sagdusmir/G32-Grill-Display-480x320-BTpref/misc/cases/Case JC3248W535C (remix) avoiding delemination with mounting option for G32 - 7295356/images/Case_JC3248W535C_with_bezel_optional_hanger.jpg

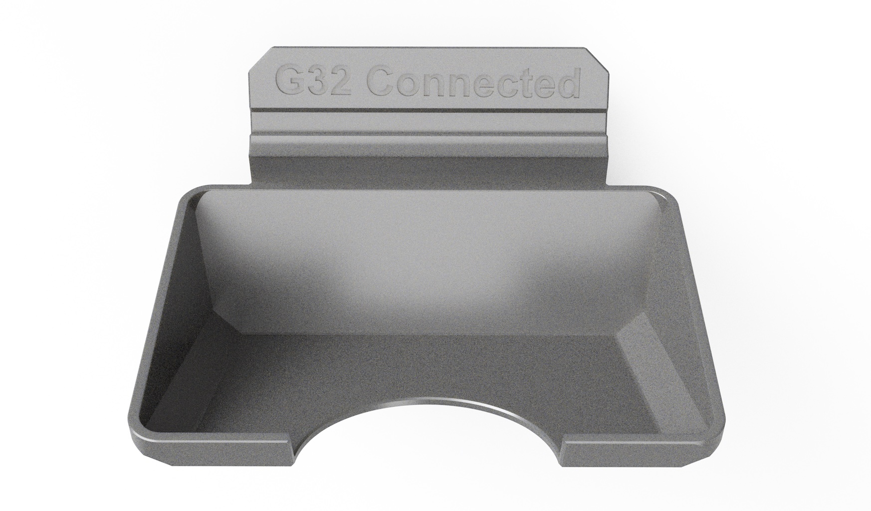
misc/cases/Case JC3248W535C (remix) avoiding delemination with mounting option for G32 - 7295356/images/Case_JC3248W535C_with_bezel_optional_hanger.jpg
