sagdusmir/G32-Grill-Display-480x320-BTpref/misc/cases/Case JC3248W535C (remix) avoiding delemination with mounting option for G32 - 7295356/images/IMG_0335.jpeg

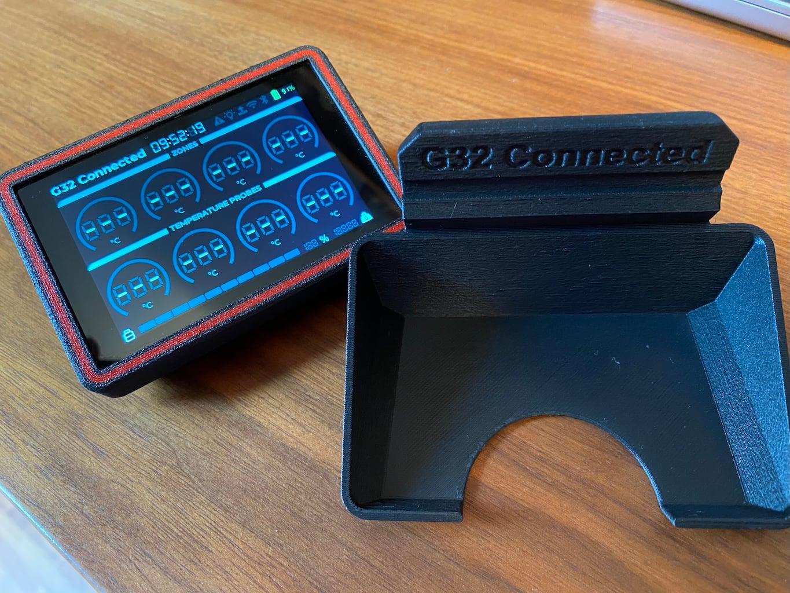
misc/cases/Case JC3248W535C (remix) avoiding delemination with mounting option for G32 - 7295356/images/IMG_0335.jpeg
