sagdusmir/G32-Grill-Display-480x320-BTpref/misc/cases/Case JC3248W535C (remix) with mounting option to G32 or compatible modules - 7182655/images/IMG_0139.jpeg

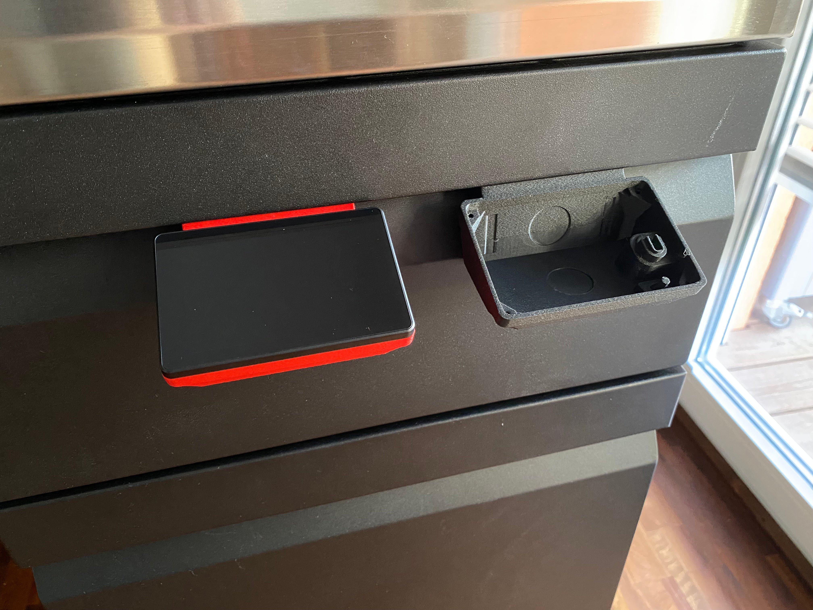
misc/cases/Case JC3248W535C (remix) with mounting option to G32 or compatible modules - 7182655/images/IMG_0139.jpeg
