sagdusmir/G32-Grill-Display-480x320-BTpref/misc/JC3248W535.jpeg

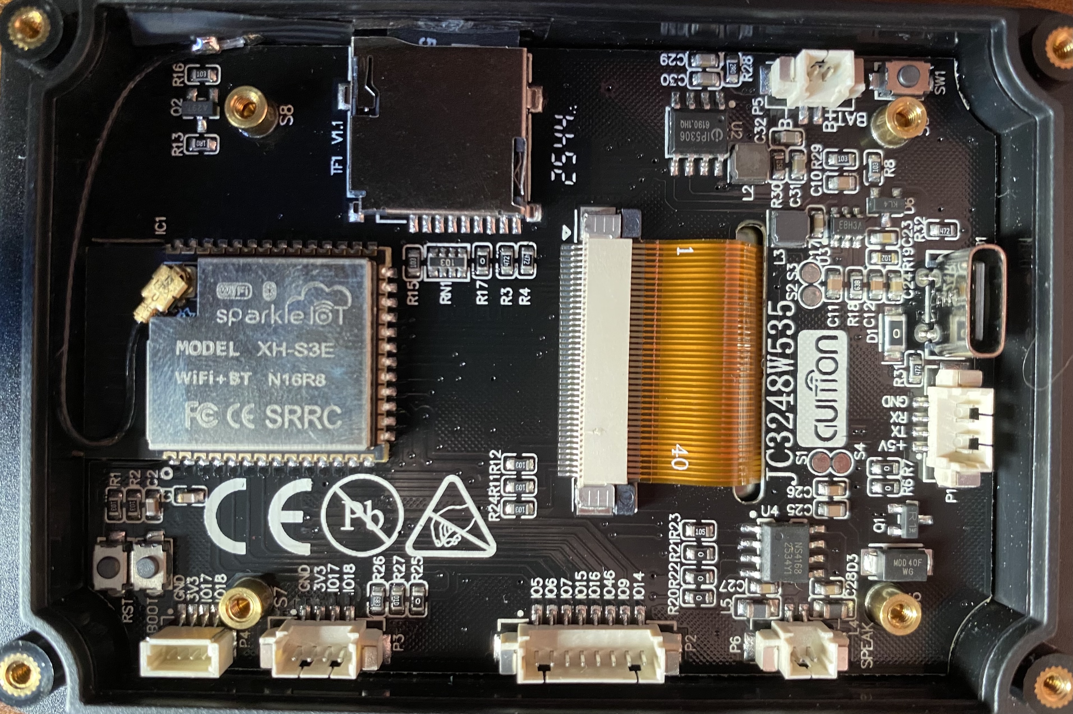
misc/JC3248W535.jpeg
