sagdusmir/G32-Grill-Display-480x320-BTpref/g32-display.yaml

substitutions:
  # # # # # # # # # # # # # # # # # # # # # # # # # # # # # # # # # # # # # # # # #
  # You will propably need to do changes only to the following lines (if at all): #
  # # # # # # # # # # # # # # # # # # # # # # # # # # # # # # # # # # # # # # # # #

  # Possible chages you might want to do to this yaml
  # -------------------------------------------------
  
  # api_encryption_key:
  # This can only changed by editing this file.
  # This value is required to connect your device to a Homa Assistant installation.
  # If you choose to change this value, you would need to do that every time you
  # upload a new software version. If you trust the other users of your WiFi, this
  # is probably unnecessary because this software does not create a fallback Access Point
  # with a default password.

  # ota_password:
  # This CAN be changed afterwards (not recommended) but any malicious attacker would need
  # to have access to your WiFi.
  # If you changed that value on the device, you will need to also update the value in this file
  # to get OTA updates working. The device uses this value as a default but also remembers the
  # last setting.
  # Same as above: only bother changing it if you really feel the need to do so.

  # FORCE_SHADOW_COLOR_TO_BLACK:
  # If the "shadow" of icons and numerical values annoy you, set this to 'true' to make it
  # disappear for all color schemes.
  # The color scheme "white (clean)" gives you an example how this would look like.

  # COLOR_SCHEMES
  # You can add your own color scheme – or remove existing ones that you don't like.
  # Columns are explained right above the COLOR_SCHEMES substitution.
  
  # General information for customizing optional hardware:
  # Speaker / Buzzer:
  # By default the buzzer is pre-configured. See two config blocks "RTTTL buzzer (GPIO pin)".
  # Configuration for a speaker is disabled. See two config blocks "RTTTL speaker (speaker header, external DAC)"
  # Just (un-)/comment the config blocks for the hardware you would like to use.

  # Name of the ESPHome device (modify if you like, avoid special characters)
  name: g32-display-bt90
  device_description: "Monitor an OW G32 grill"
  version: "BTpref-retro 2.5.7-1"
  url_qrcode: "https://github.com/sagdusmir/G32-Grill-Display-480x320-BTpref"
  url_check_for_updates: "https://api.github.com/repos/sagdusmir/G32-Grill-Display-480x320-BTpref/releases/latest"

  # Enter data of the newly created Home Assistant ESPHome device. Example:
  api_encryption_key: "E1fyywUUE1DWzu0OzhDkyc4yAnfGwyEfsVNvhytrU6k="

  # over-the-air updates (ESPHome CLI or Home Assistant add-On)
  # Hint: if you changed this value on the device, you might have to alter
  # this value here to match it. esphome cli uses the value from the yaml for the ota update!
  ota_password: "7fdf9f656d36180bfba92d596c9e7db3"

  # Some color themes:
  #
  # All consist of a primary color and three additional
  # colors of reduced luminocity.
  # -> color_100, ... color_25
  #
  # The next one lets you define a dedicated color for shadows of symbols and text.
  # Set this color as dark as you need. To have this set to black for all color schemes
  # simply use the FORCE_SHADOW_COLOR_TO_BLACK substitution.
  # -> color_00
  #
  # In addition to that, there is a "good" and a "bad"
  # color. For a less colorful UI you could just use
  # the primary color for "good", too. But I suggest
  # having a popping color for the "bad" stuff.
  # -> color_good, color_bad
  #
  # Last but not least, there is a separate color for
  # the light bulb symbol...which I usually do not change.
  # -> color_light
  #
  # The idx column is important and used to identify the select color theme.

  COLOR_SCHEMES: |
    //                  idx 100%      75%       50%       25%       <=25%    GOOD      BAD       LIGHT
    {
      {"white",         {0, 0xffffff, 0xbfbfbf, 0x808080, 0x404040, 0x404040, 0x8bff85, 0xff5757, 0xffff00}},
      {"amber",         {1, 0xffb900, 0xbd8a00, 0x805d00, 0x392900, 0x392900, 0x58b100, 0xff5600, 0xffff00}},
      {"cyan",          {2, 0x68e2fb, 0x00acbf, 0x007582, 0x003c43, 0x003c43, 0x75fb8a, 0xea838d, 0xffff00}},
      {"night red",     {3, 0xff0059, 0xc00044, 0x80002e, 0x400018, 0x400018, 0xff0059, 0xe4d300, 0xffff00}},
      {"green",         {4, 0x06bd00, 0x058d00, 0x046f00, 0x003008, 0x003008, 0x00ff00, 0xfe3a03, 0xffff00}},
      {"night blue",    {5, 0x1a00ff, 0x1300b6, 0x0d007a, 0x040028, 0x040028, 0x00ff4d, 0xff0092, 0xffff00}},
      {"purple",        {6, 0xff00e4, 0xc000ac, 0x800073, 0x32002d, 0x32002d, 0x00ffb0, 0xff1100, 0xffff00}},
      {"yellow",        {7, 0xffda00, 0xbea300, 0x806d00, 0x262000, 0x262000, 0x64dc00, 0xff5900, 0xffff00}},
      {"white (clean)", {8, 0xffffff, 0xbfbfbf, 0x808080, 0x404040, 0x000000, 0x8bff85, 0xff5757, 0xffff00}}
    }

  FORCE_SHADOW_COLOR_TO_BLACK: 'false'  # standard: use COLOR_00 for shadows
  # FORCE_SHADOW_COLOR_TO_BLACK: 'true'  # alternative: symbol and text shadows should not be visible

  # max temperature for zones and sensors
  Zone_Max: "500"
  Sensor_Max: "100"

  # interval for alarm sound
  Beeper_interval: "5s"

  # Meater protection alerts
  meater_tip_alert: '100'  # Specs: 100°C (original Meater: 100°C, 105°C (Meater PRO - not supported yet)
  meater_ambient_alert: '270'  # Specs: 275°C (original Meater), 550°C (Meater PRO - not supported yet)

  # sounds (in RTTTL syntax):
  G32_Connect_Sound: "pling2:d=16,o=6,b=140:e6,32p,d6"
  G32_Disconnect_Sound: "siren:d=8,o=5,b=100:d,e,d,e,d,e,d,e"
  MT_Connect_Sound: "Pling4:d=16,o=5,b=100:a5,32p,a6"
  MT_Disconnect_Sound: "plonk:d=16,o=5,b=100:a6,32p,a5"
  Wifi_Connect_Sound: "dadi:d=16,o=6,b=140:d6,32p,e6"
  Wifi_Disconnect_Sound: "siren:d=8,o=5,b=100:d,e,d,e,d,e,d,e"
  Timer_Alarm_Sound: "didididi:d=16,o=6,b=140:e6,32p,e6,32p,e6,32p,e6"
  Zone_Limit_Alarm_Sound: "dadidadi:d=8,o=5,b=150:d,e,d,e,d,e,d,e"
  Sensor_Limit_Alarm_Sound: "didadida:d=8,o=5,b=150:e,d,e,d,e,d,e,d"
  New_MAC_Sound: "click:d=32,o=6,b=120:32c,32p"

  # D A N G E R  Z O N E! # # # # # # # # # # # # # # # # # # # # # # # # # # # # 
  # From here on, please only make changes if you know what you are doing and   #
  # have an idea of what you want to achieve. :)                                #
  # # # # # # # # # # # # # # # # # # # # # # # # # # # # # # # # # # # # # # # #

  g32_mac_address: 94:E6:86:00:00:00
  g32_service_uuid: dc0f41ea-b6ae-46a8-a19e-1a3bf4342bcb
  g32_characteristic_uuid_tx: 'dc0f41e2-b6ae-46a8-a19e-1a3bf4342bcb'
  # g32_characteristic_uuid_rx: 'dc0f41e1-b6ae-46a8-a19e-1a3bf4342bcb'  # from the original OW app

  wifi_ssid: "wifi_ssid"
  wifi_password: "password"

  meater_mac_address: B8:1F:5E:00:00:00
  meater_service_uuid: 'a75cc7fc-c956-488f-ac2a-2dbc08b63a04'
  meater_characteristic_uuid_temp: '7edda774-045e-4bbf-909b-45d1991a2876'
  meater_characteristic_uuid_battery: '2adb4877-68d8-4884-bd3c-d83853bf27b8'

  Invalid_Sensor_Value: '1500'  # 1500 (and above) means "invalid"

  # shades of white (initial start values since substitutions work best)
  COLOR_100:   "0xffffff"  # 100% brightness
  COLOR_75:    "0xbfbfbf"  #  75%
  COLOR_50:    "0x808080"  #  50%
  COLOR_25:    "0x404040"  #  25%
  COLOR_00:    "0x404040"  # shadows
  COLOR_GOOD:  "0x8bff85"
  COLOR_BAD:   "0xff5757"
  COLOR_LIGHT: "0xffff00"

  # MEATER tip raw is 12-bit two's complement, little-endian. °C = (raw + 8) / 16.
  # Unsigned 0x0FE8 is 255°C; sign-extended it is -1°C. A 16-bit signed payload
  # (0xFFE8) is already negative after the int16_t cast, so leave it alone.
  meater_decode_tip: |-
    uint16_t tip_u = uint16_t(x[0]) | (uint16_t(x[1]) << 8); int16_t tip = int16_t(tip_u); if (tip_u < 0x1000 && tip >= 2048) tip -= 4096;

esphome:
  name: ${name}
  build_path: /tmp/esphome_build/${name}
  min_version: "2026.8.2"
  platformio_options:
    upload_speed: 921600
    board_build.flash_mode: dio
    board_build.f_flash: 80000000L
    board_build.f_cpu: 240000000L

  project:
    name: "g32.bt_display480_320"
    version: ${version}

  on_boot:
    priority: 1100 # stay above 1000 and below 1500!
    then:
      - lambda: id(boot_start_time) = millis();
                // the following line prevents the wifi password
                // from being shown - but makes it nearly impossible
                // to enter a complex password at all.
                // lv_textarea_set_password_show_time(id(settings_wifi_password_textarea), 0);  # 0 ms = hide immediately

esp32:
  board: esp32-s3-devkitc-1
  # variant: esp32S3  # use either board: or variant
  flash_size: 16MB
  cpu_frequency: 160MHZ  # esphome 2026.4.0 uses by default 240MHZ
  framework:
    type: esp-idf
    sdkconfig_options:
      # CONFIG_ESP_TASK_WDT_EN: "n" # Disables Task Watchdog Timer (TWDT)
      CONFIG_ESP_INT_WDT: "n"      # Disables Interrupt Watchdog Timer (IWDT)
      # COMPILER_OPTIMIZATION_SIZE: "y"  # optimize for size
      CONFIG_COMPILER_OPTIMIZATION_PERF: "y"
      CONFIG_ESP32S3_DEFAULT_CPU_FREQ_240: "y"
      CONFIG_ESP32S3_DATA_CACHE_64KB: "y"
      CONFIG_ESP32S3_DATA_CACHE_LINE_64B: "y"
      CONFIG_SPIRAM_FETCH_INSTRUCTIONS: "y"
      CONFIG_SPIRAM_RODATA: "y"
      CONFIG_ESP_WIFI_TASK_CORE_ID: "0"
      CONFIG_BT_BTC_TASK_CORE_ID: "0"
      CONFIG_BT_NIMBLE_PINNED_TO_CORE: "0"
      CONFIG_TCPIP_TASK_CORE_ID: "0"
      CONFIG_ESP_TIMER_TASK_CORE_ID: "0"
      CONFIG_ESP_MAIN_TASK_AFFINITY_CPU1: "y"

psram:
  mode: octal
  speed: 80MHz # 120mhz is not supported and falls back to 40mhz

logger:
  # baud_rate: 921600  # enable logging
  baud_rate: 0  # no logging -> saves power

api: # enable Home Assistant API
  encryption:
    key: ${api_encryption_key}
  reboot_timeout: 0s  

http_request:
  # optional global defaults (recommended for reliability)
  timeout: 5s
  verify_ssl: true
  follow_redirects: true

ota:
  - platform: esphome
    id: my_ota
    password: ${ota_password}

wifi:
  id: my_wifi
  ssid: ${wifi_ssid}  # must be dynamically applied later
  password: ${wifi_password}  # must be dynamically applied later
  fast_connect: True
  reboot_timeout: 0s
  on_connect:
    then:
      - rtttl.play: ${Wifi_Connect_Sound}
      - lambda: |-
          id(current_ip_address) = id(wifi_ip_sensor).state.c_str();
      - globals.set:
          id: wifi_connected
          value: 'true'
      - globals.set:
          id: apply_wifi_started_by_user
          value: 'false'
      - lvgl.widget.refresh: wifi_connect_label
      - lvgl.widget.refresh: current_wifi_ip_label
      - script.execute: check_for_updates

  on_disconnect:
    then:
      - if: # no sound if user updated credentials
          condition:
            - lambda: |-
                return !(id(apply_wifi_started_by_user));
          then:
            - rtttl.play: ${Wifi_Disconnect_Sound}
      - globals.set:
          id: wifi_connected
          value: 'false'
      - globals.set:
          id: current_ip_address
          value: '" "'  # not connected
      - lvgl.widget.refresh: wifi_connect_label
      - lvgl.widget.refresh: current_wifi_ip_label
esp32_ble:
  # 1xG32, 4xMeater probes -> maximum 5 connections needed
  max_connections: 5  # new option since 2025.10.15, used to be under the esp32_ble_tracker component

esp32_ble_tracker:
  # 1xG32, 4xMeater probes -> maximum 5 connections needed
  # max_connections: 5  # up till esphome 2025.9.1. now moved to esp32_ble component.
  on_ble_advertise:
    then:
      - lambda: |-
          char mac_buf[MAC_ADDRESS_PRETTY_BUFFER_SIZE];

          if (x.get_name().starts_with("OWG-G32C") && id(ble_g32_scan_started_by_user)) {
            x.address_str_to(mac_buf);
            id(settings_g32_mac_address) = mac_buf;
            lv_obj_clear_flag(id(settings_mac_address_updated), LV_OBJ_FLAG_HIDDEN);
            id(my_rtttl).play("${New_MAC_Sound}");
            ESP_LOGI("ble_adv", "G32 MAC address: %s", mac_buf);
            id(ble_g32_scan_stop).execute();
          }

          if ((x.get_name() == "MEATER" || x.get_name() == "MEATER+") && id(ble_meater_scan_started_by_user)) {
            if (id(ble_meaters_found) < 15) {
              if (!x.get_manufacturer_datas().empty() && !x.get_manufacturer_datas()[0].data.empty()) {  // assert data is available
                int probe_id = x.get_manufacturer_datas()[0].data[0];  // first data byte

                // for solo meaters without probe ID (issue reported by @JBecker32)
                if (probe_id == 0) {
                  probe_id = 1;
                }

                if (probe_id > 0 && probe_id < 5) {
                  int idx = probe_id-1;
                  if ((id(ble_meaters_found) & (1 << idx)) == 0) {
                    id(ble_meaters_found) |= (1 << idx);
                    id(my_rtttl).play("${New_MAC_Sound}");
                    x.address_str_to(mac_buf);
                    ESP_LOGI("ble_adv", "Meater MAC address: %s", mac_buf);
                    id(settings_meater_mac_addresses)[idx] = mac_buf;
                    std::array<lv_obj_t *, 4> meater_labels = {id(settings_meater0_label), id(settings_meater1_label), id(settings_meater2_label), id(settings_meater3_label)};
                    std::array<lv_obj_t *, 4> meater_updated = {id(settings_meater0_updated), id(settings_meater1_updated), id(settings_meater2_updated), id(settings_meater3_updated)};
                    lv_obj_clear_flag(meater_updated[idx], LV_OBJ_FLAG_HIDDEN);
                    lv_label_set_text(meater_labels[idx], mac_buf);
                  }
                }
              }
            }
            if (id(ble_meaters_found) >= 15) {
              id(ble_meater_scan_stop).execute();           
            }
          } 

          // some logging
          // if (x.get_name().starts_with("OWG-G32C")) {
          //   ESP_LOGI("ble_adv", "G32 found");
          //   ESP_LOGI("ble_adv", "  Name: %s", x.get_name().c_str());
          //   ESP_LOGI("ble_adv", "  MAC address: %s", x.address_str_to(mac_buf));
          // }
          // if (x.get_name().starts_with("MEATER+")) {
          //   ESP_LOGI("ble_adv", "Meater+ found");
          //   ESP_LOGI("ble_adv", "  Name: %s", x.get_name().c_str());
          //   ESP_LOGI("ble_adv", "  MAC address: %s", x.address_str_to(mac_buf));
          // }
          // if (x.get_name() == "MEATER") {
          //   ESP_LOGI("ble_adv", "Meater found");
          //   ESP_LOGI("ble_adv", "  Name: %s", x.get_name().c_str());
          //   ESP_LOGI("ble_adv", "  MAC address: %s", x.address_str_to(mac_buf));
          // }
          // if (x.get_name() == "MEATER BLOCK") {
          //   ESP_LOGI("ble_adv", "Meater Block found");
          //   ESP_LOGI("ble_adv", "  Name: %s", x.get_name().c_str());
          //   ESP_LOGI("ble_adv", "  MAC address: %s", x.address_str_to(mac_buf));
          // }

          // log everything we get on advertise
          if (0) {
            ESP_LOGD("ble_adv", "New BLE device");
            ESP_LOGD("ble_adv", "  address: %s", x.address_str_to(mac_buf));
            ESP_LOGD("ble_adv", "  RSSI: %d", x.get_rssi());
            ESP_LOGD("ble_adv", "  name: %s", x.get_name().c_str());
            ESP_LOGD("ble_adv", "  Advertised service UUIDs:");
            for (auto uuid : x.get_service_uuids()) {
              char uuid_buf[37];
              ESP_LOGD("ble_adv", "    - %s", uuid.to_str(uuid_buf));
            }
            ESP_LOGD("ble_adv", "  Advertised service data:");
            for (auto data : x.get_service_datas()) {
              char uuid_buf[37];
              ESP_LOGD("ble_adv", "    - %s: (length %i)", data.uuid.to_str(uuid_buf), data.data.size());
              // To log the actual data bytes, you can add a loop here
              std::string hex_data;
              for (auto byte : data.data) {
                  char buf[3];
                  sprintf(buf, "%02X ", byte);
                  hex_data += buf;
                }
              ESP_LOGD("ble_adv", "      data: %s", hex_data.c_str());
            }
            ESP_LOGD("ble_adv", "  Advertised manufacturer data:");
            for (auto data : x.get_manufacturer_datas()) {
              char uuid_buf[37];
              ESP_LOGD("ble_adv", "    - %s: (length %i)", data.uuid.to_str(uuid_buf), data.data.size());
              // Similarly, log the data bytes
              std::string hex_data;
              for (auto byte : data.data) {
                  char buf[3];
                  sprintf(buf, "%02X ", byte);
                  hex_data += buf;
                }
              ESP_LOGD("ble_adv", "      data: %s", hex_data.c_str());
            }
          }


      - lvgl.widget.refresh: settings_mac_address_label
      - lvgl.widget.refresh: [settings_meater0_label, settings_meater1_label, settings_meater2_label, settings_meater3_label]

ble_client:
  - mac_address: ${g32_mac_address}  # must be dynamically applied later
    id: ow_g32
    on_connect:
      then:
        - rtttl.play: ${G32_Connect_Sound}
        - globals.set:
            id: g32_connected
            value: 'true'
        - lvgl.widget.refresh: g32bt_connect_label
    on_disconnect:
      then:
        - rtttl.play: ${G32_Disconnect_Sound}
        - globals.set:
            id: g32_connected
            value: 'false'
        - lvgl.widget.refresh: g32bt_connect_label
        - globals.set:
            id: gas_weight
            value: '-1'
        - lvgl.widget.refresh: gas_weight_label
        - globals.set:
            id: gas_percent
            value: '0'
        - lvgl.widget.refresh: [gas_percent_label, gas_percent_label_unit, gas_percent_bar]
        - globals.set:
            id: zone1_value
            value: ${Invalid_Sensor_Value}
        - globals.set:
            id: zone2_value
            value: ${Invalid_Sensor_Value}
        - globals.set:
            id: zone3_value
            value: ${Invalid_Sensor_Value}
        - globals.set:
            id: zone4_value
            value: ${Invalid_Sensor_Value}
        - globals.set:
            id: sensor1_value
            value: ${Invalid_Sensor_Value}
        - globals.set:
            id: sensor2_value
            value: ${Invalid_Sensor_Value}
        - globals.set:
            id: sensor3_value
            value: ${Invalid_Sensor_Value}
        - globals.set:
            id: sensor4_value
            value: ${Invalid_Sensor_Value}
        - globals.set:
            id: active_sensors
            value: "0"
        - script.execute: refresh_all_temps

  - mac_address: ${meater_mac_address}
    id: meater0
    on_connect:
      then:
        - lambda: |-
            id(active_meaters) |= 0x01;
            id(meater_alarms_tip) |= 0x01;
            id(meater_alarms_ambient) |= 0x01;
        - rtttl.play: ${MT_Connect_Sound}
    on_disconnect:
      then:
        - lambda: |-
            id(active_meaters) &= ~0x01;
            id(meater_alarms_tip) &= ~0x01;
            id(meater_alarms_ambient) &= ~0x01;
        - lambda: |-
            id(g32_probe1).publish_state(${Invalid_Sensor_Value});
        - rtttl.play: ${MT_Disconnect_Sound}
        - script.execute: refresh_all_meater_alerts
  - mac_address: ${meater_mac_address}
    id: meater1
    on_connect:
      then:
        - lambda: |-
            id(active_meaters) |= 0x02;
            id(meater_alarms_tip) |= 0x02;
            id(meater_alarms_ambient) |= 0x02;
        - rtttl.play: ${MT_Connect_Sound}
    on_disconnect:
      then:
        - lambda: |-
            id(active_meaters) &= ~0x02;
            id(meater_alarms_tip) &= ~0x02;
            id(meater_alarms_ambient) &= ~0x02;
        - lambda: |-
            id(g32_probe2).publish_state(${Invalid_Sensor_Value});
        - rtttl.play: ${MT_Disconnect_Sound}
        - script.execute: refresh_all_meater_alerts
  - mac_address: ${meater_mac_address}
    id: meater2
    on_connect:
      then:
        - lambda: |-
            id(active_meaters) |= 0x04;
            id(meater_alarms_tip) |= 0x04;
            id(meater_alarms_ambient) |= 0x04;
        - rtttl.play: ${MT_Connect_Sound}
    on_disconnect:
      then:
        - lambda: |-
            id(active_meaters) &= ~0x04;
            id(meater_alarms_tip) &= ~0x04;
            id(meater_alarms_ambient) &= ~0x04;
        - lambda: |-
            id(g32_probe3).publish_state(${Invalid_Sensor_Value});
        - rtttl.play: ${MT_Disconnect_Sound}
        - script.execute: refresh_all_meater_alerts
  - mac_address: ${meater_mac_address}
    id: meater3
    on_connect:
      then:
        - lambda: |-
            id(active_meaters) |= 0x08;
            id(meater_alarms_tip) |= 0x08;
            id(meater_alarms_ambient) |= 0x08;
        - rtttl.play: ${MT_Connect_Sound}
    on_disconnect:
      then:
        - lambda: |-
            id(active_meaters) &= ~0x08;
            id(meater_alarms_tip) &= ~0x08;
            id(meater_alarms_ambient) &= ~0x08;
        - lambda: |-
            id(g32_probe4).publish_state(${Invalid_Sensor_Value});
        - rtttl.play: ${MT_Disconnect_Sound}
        - script.execute: refresh_all_meater_alerts

#-------------------------------------------
# Display qspi
#-------------------------------------------
spi:
  id: display_qspi
  type: quad
  clk_pin: 47
  data_pins: [21, 48, 40, 39]

display:
  # - platform: mipi_spi
  #   model: axs15231  # JC4832W535 or axs15231 / JC3248W535C variant
  - platform: qspi_dbi
    model: JC4832W535
    data_rate: 40MHz
    id: my_display
    spi_id: display_qspi
    dimensions:
      height: 480
      width: 320
    cs_pin:
      number: 45
      ignore_strapping_warning: true
    auto_clear_enabled: false  # has to be set to 'false' for lvgl
    update_interval: never  # LVGL handles rendering

#-------------------------------------------
# Touchscreen gt911 i2c
#-------------------------------------------
i2c:
  - id: touchscreen_bus
    sda: GPIO4
    scl: GPIO8
    scan: false

touchscreen:
  - platform: axs15231
    id: my_touchscreen
    display: my_display
    i2c_id: touchscreen_bus
    # for test purposes, touch coordinates can be logged
    # on_touch:
    #   - lambda: |-
    #       ESP_LOGI("cal", "x=%d, y=%d, x_raw=%d, y_raw=%0d",
    #         touch.x,
    #         touch.y,
    #         touch.x_raw,
    #         touch.y_raw
    #       );
    on_release:
      - if:
          condition: lvgl.is_paused
          then:
            - logger.log: "Display is resuming"
            - lvgl.resume:
            - lvgl.widget.redraw:
            - light.turn_on: backlight

#---------------------------------------------
# RTTTL speaker (speaker header, external DAC)
#---------------------------------------------
# i2s_audio:                               # variant [speaker] 
#   # external DAC: NS4168                 # variant [speaker] 
#   i2s_lrclk_pin: GPIO02                  # variant [speaker] 
#   i2s_bclk_pin: GPIO42                   # variant [speaker] 
# speaker:                                 # variant [speaker] 
#   - platform: i2s_audio                  # variant [speaker]
#     id: my_speaker                       # variant [speaker] 
#     dac_type: external                   # variant [speaker] 
#     i2s_dout_pin: GPIO41                 # variant [speaker] 
#     channel: mono                        # variant [speaker] 
#     buffer_duration: 0.1s                # variant [speaker] 
#-------------------------------------------
# Internal outputs
#-------------------------------------------
output:
  - platform: ledc
    id: gpio_backlight_pwm
    pin: 1


    #-------------------------------------------
    # RTTTL buzzer (GPIO pin)
    #-------------------------------------------
  - id: helper_low_beeper              # variant [buzzer]
    platform: ledc                     # variant [buzzer]
    pin: 14                            # variant [buzzer]
  - platform: ledc                     # variant [buzzer]
    pin: 9                             # variant [buzzer]
    id: rtttl_out                      # variant [buzzer]
#-------------------------------------------
# Internal lights
#-------------------------------------------
light:
  - id: backlight
    name: Backlight
    platform: monochromatic
    output: gpio_backlight_pwm
    restore_mode: ALWAYS_ON

rtttl:
  id: my_rtttl

  #-------------------------------------------
  # RTTTL buzzer (GPIO pin)
  #-------------------------------------------
  output: rtttl_out                      # variant [buzzer]
  gain: 80%                              # variant [buzzer]

  #-------------------------------------------
  # RTTTL speaker (speaker header, external DAC)
  #-------------------------------------------
  # speaker: my_speaker                    # variant [speaker] 
  # gain: 100%                             # variant [speaker] 
interval:
  - interval: 1s
    then:
      - script.execute: timer_update
  - interval: 10s
    then:
      - lvgl.widget.refresh: warning_on_label
  - interval: ${Beeper_interval}
    then:
      - lambda: |-
          if( ((id(zone1_limit_value) > 0) && (id(zone1_value) >= id(zone1_limit_value)))
           || ((id(zone2_limit_value) > 0) && (id(zone2_value) >= id(zone2_limit_value)))
           || ((id(zone3_limit_value) > 0) && (id(zone3_value) >= id(zone3_limit_value)))
           || ((id(zone4_limit_value) > 0) && (id(zone4_value) >= id(zone4_limit_value)))
           || id(meater_alarms_ambient) > 0 || id(meater_alarms_tip) > 0 ) {
            id(my_rtttl).play("${Zone_Limit_Alarm_Sound}");
          }
          else if ( ((id(sensor1_limit_value) > 0) && (id(sensor1_value) >= id(sensor1_limit_value)))
                 || ((id(sensor2_limit_value) > 0) && (id(sensor2_value) >= id(sensor2_limit_value)))
                 || ((id(sensor3_limit_value) > 0) && (id(sensor3_value) >= id(sensor3_limit_value)))
                 || ((id(sensor4_limit_value) > 0) && (id(sensor4_value) >= id(sensor4_limit_value))) ) {
            id(my_rtttl).play("${Sensor_Limit_Alarm_Sound}");
          }
          else if( id(timer_alarm) == true ) {
            id(my_rtttl).play("${Timer_Alarm_Sound}");
          }
  - interval: 1s
    then:
      - if:
          condition:
            and:
              - lambda: return !id(boot_screen_color_scheme_init);
          then:
            - lambda: |-
                id(boot_screen_color_scheme_init) = true;
                id(settings_color_scheme_idx) = id(settings_color_scheme_idx_persistent);
                id(apply_color_scheme).execute();

      - if:
          condition:
            and:
              - lambda: 'return !id(boot_screen_hidden);'
              - lambda: 'return millis() - id(boot_start_time) >= 2000;'
          then:
            - script.execute: hide_boot_screen

#-------------------------------------------
# Global varaibles
#-------------------------------------------
globals:
  - id: wifi_connected
    type: bool
    initial_value: 'false'
  - id: g32_connected
    type: bool
    initial_value: 'false'
  - id: firebox_open
    type: bool
    initial_value: 'false'
  - id: light_on
    type: bool
    initial_value: 'false'
  - id: warning_on
    type: bool
    initial_value: 'false'
  - id: gas_weight
    type: int32_t
    initial_value: '-1'
  - id: gas_percent
    type: int32_t
    initial_value: '0'
  - id: ble_g32_scan_started_by_user  # for managing "scan" button status
    type: bool
    initial_value: 'false'
  - id: ble_meater_scan_started_by_user  # for managing "scan" button status
    type: bool
    initial_value: 'false'
  - id: ble_meaters_found  # bits set/reset for every active/inactive Meater probe
    type: int
    initial_value: '0'
  - id: apply_wifi_started_by_user  # for supressing sounds
    type: bool
    initial_value: 'false'
  - id: flag_wifi_updated  # helper to know if wifi needs to be applied
    type: bool
    initial_value: 'true'
  - id: flag_ota_updated  # helper to know if ota needs to be applied
    type: bool
    initial_value: 'true'

  - id: settings_wifi_ssid_persistent
    type: std::string
    restore_value: true
    initial_value: '"${wifi_ssid}"'
    max_restore_data_length: 33  # max SSID length: 32
  - id: settings_wifi_ssid
    type: std::string
    initial_value: " "
  - id: settings_wifi_password_persistent
    type: std::string
    restore_value: true
    initial_value: '"${wifi_password}"'
    max_restore_data_length: 65  # max password length: 64
  - id: settings_wifi_password
    type: std::string
    initial_value: " "
  - id: settings_ota_password_persistent
    type: std::string
    restore_value: true
    initial_value: '"${ota_password}"'
    max_restore_data_length: 65  # max password length: 64
  - id: settings_ota_password
    type: std::string
    initial_value: '""'

  - id: color_schemes
    type: std::map<std::string, std::vector<uint32_t>>
    initial_value: '${COLOR_SCHEMES}'
  - id: color_100
    type: int
    initial_value: '0x000000'
  - id: color_75
    type: int
    initial_value: '0x000000'
  - id: color_50
    type: int
    initial_value: '0x000000'
  - id: color_25
    type: int
    initial_value: '0x000000'
  - id: color_00
    type: int
    initial_value: '0x000000'
  - id: color_good
    type: int
    initial_value: '0x000000'
  - id: color_bad
    type: int
    initial_value: '0x000000'
  - id: color_light
    type: int
    initial_value: '0x000000'

  - id: boot_start_time
    type: uint32_t
    initial_value: '0'
  - id: boot_screen_hidden
    type: bool
    initial_value: 'false'
  - id: boot_screen_color_scheme_init
    type: bool
    initial_value: 'false'
  - id: latest_version
    type: std::string
    initial_value: '"${version}"'

  - id: active_sensors      # bits set/reset for every active/inactive Sensor
    type: int
    initial_value: '0'

  - id: active_meaters      # bits set/reset for every active/inactive Meater probe
    type: int
    initial_value: '0'

  - id: zone1_value         # the value used for zone temperature labels and arcs
    type: int
    initial_value: ${Invalid_Sensor_Value}
  - id: zone2_value
    type: int
    initial_value: ${Invalid_Sensor_Value}
  - id: zone3_value
    type: int
    initial_value: ${Invalid_Sensor_Value}
  - id: zone4_value
    type: int
    initial_value: ${Invalid_Sensor_Value}

  - id: sensor1_value       # the value used for sensor temperature labels and arcs
    type: int
    initial_value: ${Invalid_Sensor_Value}
  - id: sensor2_value
    type: int
    initial_value: ${Invalid_Sensor_Value}
  - id: sensor3_value
    type: int
    initial_value: ${Invalid_Sensor_Value}
  - id: sensor4_value
    type: int
    initial_value: ${Invalid_Sensor_Value}

  - id: zone1_limit_value   # the value used for zone limit labels and arcs
    type: int
    initial_value: '0'
  - id: zone2_limit_value
    type: int
    initial_value: '0'
  - id: zone3_limit_value
    type: int
    initial_value: '0'
  - id: zone4_limit_value
    type: int
    initial_value: '0'

  - id: sensor1_limit_value # the value used for sensor limit labels and arcs
    type: int
    initial_value: '0'
  - id: sensor2_limit_value
    type: int
    initial_value: '0'
  - id: sensor3_limit_value
    type: int
    initial_value: '0'
  - id: sensor4_limit_value
    type: int
    initial_value: '0'

  - id: meater_values_tip
    type: std::array<float, 4>
    initial_value: '{0.0,0.0,0.0,0.0}'
  - id: meater_values_ambient
    type: std::array<float, 4>
    initial_value: '{0.0,0.0,0.0,0.0}'
  - id: meater_values_battery
    type: std::array<int, 4>
    initial_value: '{100,100,100,100}'


  - id: meater_tip_alert
    type: float
    initial_value: '${meater_tip_alert}'
  - id: meater_ambient_alert
    type: float
    initial_value: '${meater_ambient_alert}'
  - id: meater_alarms_tip  # bits set/reset
    type: int
    initial_value: '0'
  - id: meater_alarms_ambient  # bits set/reset
    type: int
    initial_value: '0'

  - id: battery_soc_value
    type: int
    initial_value: '0'

  - id: sensor_index        # parameter for zone (1-4) or sensor (5-8)
    type: int
    initial_value: '0'
  - id: sensor_limit_value  # the actual sensor limit for the indexed Zone/Sensor
    type: int
    initial_value: '0'
  - id: sensor_max_value    # maximum value for zone and sensor values (arcs)
    type: int
    initial_value: '0'

  - id: timer_h             # timer hours
    type: int
    initial_value: '0'
  - id: timer_m             # timer minutes
    type: int
    initial_value: '0'
  - id: timer_s             # timer seconds
    type: int
    initial_value: '0'
  - id: timer_active        # timer active (=running)
    type: bool
    initial_value: 'false'
  - id: timer_alarm         # timer alarm active
    type: bool
    initial_value: 'false'

  - id: helper_h             # timer hours
    type: int
    initial_value: '0'
  - id: helper_m             # timer minutes
    type: int
    initial_value: '0'
  - id: helper_s             # timer seconds
    type: int
    initial_value: '0'

  - id: last_sensor_lower_digits  # set limits page
    type: int
    initial_value: '0'

  # settings: persisted and temporary values
  # stick to the _persistent value for usage.
  # the temporary value is intended for the
  # settings page only.
  - id: settings_g32_mac_address_persistent
    type: std::string
    initial_value: '"${g32_mac_address}"' 
    restore_value: true
    max_restore_data_length: 17
  - id: settings_g32_mac_address
    type: std::string
    initial_value: ""

  - id: settings_meater_mac_addresses_persistent
    type: std::string
    initial_value: '"${meater_mac_address},${meater_mac_address},${meater_mac_address},${meater_mac_address}"'
    restore_value: true
    max_restore_data_length: 72
  - id: settings_meater_mac_addresses
    type: std::array<std::string, 4>
    initial_value: '{"00:00:00:00:00:00","00:00:00:00:00:00","00:00:00:00:00:00","00:00:00:00:00:00"}'

  - id: settings_min_gas_value_persistent
    type: int
    initial_value: "20"
    restore_value: true
  - id: settings_min_gas_value
    type: int
    initial_value: '0'
  - id: settings_min_soc_value_persistent
    type: int
    initial_value: "25"
    restore_value: true
  - id: settings_min_soc_value
    type: int
    initial_value: '0'
  - id: settings_hide_soc_persistent
    type: bool
    initial_value: 'false'
    restore_value: true
  - id: settings_hide_soc
    type: bool
    initial_value: 'false'
  - id: settings_hide_gas_level_persistent
    type: bool
    initial_value: 'false'
    restore_value: true
  - id: settings_hide_gas_level
    type: bool
    initial_value: 'false'
  - id: settings_enable_temperature_limits_persistent
    type: bool
    initial_value: 'true'
    restore_value: true
  - id: settings_enable_temperature_limits
    type: bool
    initial_value: 'true'
  - id: settings_enable_auto_hiding_temperature_limits_persistent
    type: bool
    initial_value: 'false'
    restore_value: true
  - id: settings_enable_auto_hiding_temperature_limits
    type: bool
    initial_value: 'false'
  - id: settings_hide_inactive_sensors_persistent
    type: bool
    initial_value: 'false'
    restore_value: true
  - id: settings_hide_inactive_sensors
    type: bool
    initial_value: 'false'
  - id: settings_show_time_persistent
    type: bool
    initial_value: 'true'
    restore_value: true
  - id: settings_show_time
    type: bool
    initial_value: 'true'
  - id: settings_hide_timer_persistent
    type: bool
    initial_value: 'false'
    restore_value: true
  - id: settings_hide_timer
    type: bool
    initial_value: 'false'
  - id: settings_display_timeout_value_persistent
    type: int
    initial_value: '0'
    restore_value: true
  - id: settings_display_timeout_value
    type: int
    initial_value: '0'
  - id: settings_color_scheme_idx_persistent
    type: int
    initial_value: '0'
    restore_value: true
  - id: settings_color_scheme_idx
    type: int
    initial_value: '0'

  - id: current_ip_address
    type: std::string
    initial_value: '" "'  # not connected

text_sensor:
  - platform: wifi_info
    ip_address:
      id: wifi_ip_sensor

  - platform: template
    name: "Software Version"
    lambda: |-
      return std::string("${version}");

font:
  - file: 'https://raw.githubusercontent.com/sagdusmir/G32-Grill-Display-480x320-BTpref/main/fonts/MaterialDesign-Webfont/materialdesignicons-webfont.ttf'
    # file: 'fonts/MaterialDesign-Webfont/materialdesignicons-webfont.ttf'
    id: ICON_FONT_24
    size: 24
    glyphs:
      - "\U000F05A9" # mdi-wifi
      - "\U000F00AF" # mdi-bluetooth
      - "\U000F12A3" # mdi-battery-high
      - "\U000F12A2" # mdi-battery-medium
      - "\U000F12A1" # mdi-battery-low
      - "\U000F008E" # mdi-battery-outline
      - "\U000F17E6" # mdi-battery-plus
      - "\U000F0208" # mdi-eye
      - "\U000F0238" # mdi-fire (used for meater)
      - "\U000F029A" # mdi-gauge
      - "\U000F1358" # mdi-propane-tank-outline
      - "\U000F002A" # mdi-alert-outline
      - "\U000F0DD0" # mdi-format-list-bulleted-square
      - "\U000F140B" # mdi-lightning-bolt
      - "\U000F050F" # mdi-thermometer
      - "\U000F1A4E" # mdi-lightbulb-on-20
      - "\U000F0D3F" # mdi-weight-grams
  - file: 'https://raw.githubusercontent.com/sagdusmir/G32-Grill-Display-480x320-BTpref/main/fonts/MaterialDesign-Webfont/materialdesignicons-webfont.ttf'
    # file: 'fonts/MaterialDesign-Webfont/materialdesignicons-webfont.ttf'
    id: ICON_FONT_18
    size: 18
    glyphs:
      - "\U000F15D7" # mdi mdi-fire-alert
  - file: 'https://raw.githubusercontent.com/sagdusmir/G32-Grill-Display-480x320-BTpref/main/fonts/MaterialDesign-Webfont/materialdesignicons-webfont.ttf'
    # file: 'fonts/MaterialDesign-Webfont/materialdesignicons-webfont.ttf'
    id: ICON_FONT_12
    size: 12
    glyphs:
      - "\U000F009A" # mdi-bell
  - file: 'https://raw.githubusercontent.com/sagdusmir/G32-Grill-Display-480x320-BTpref/main/fonts/MaterialDesign-Webfont/materialdesignicons-webfont.ttf'
    # file: 'fonts/MaterialDesign-Webfont/materialdesignicons-webfont.ttf'
    id: ICON_FONT_14
    size: 14
    glyphs:
      - "\U000F051B" # mdi-timer-outline
  - file: 'https://raw.githubusercontent.com/sagdusmir/G32-Grill-Display-480x320-BTpref/main/fonts/DESG07/DSEG7ClassicMini-Bold.ttf'
    # file: 'fonts/DESG07/DSEG7ClassicMini-Bold.ttf'
    id: SEGMENT_FONT_35
    size: 35
    glyphs:
      - "0"
      - "1"
      - "2"
      - "3"
      - "4"
      - "5"
      - "6"
      - "7"
      - "8"
      - "9"
      - "-"
      - " "
  - file: 'https://raw.githubusercontent.com/sagdusmir/G32-Grill-Display-480x320-BTpref/main/fonts/DESG07/DSEG7ClassicMini-Bold.ttf'
    # file: 'fonts/DESG07/DSEG7ClassicMini-Bold.ttf'
    id: SEGMENT_FONT_22
    size: 22
    glyphs:
      - "0"
      - "1"
      - "2"
      - "3"
      - "4"
      - "5"
      - "6"
      - "7"
      - "8"
      - "9"
      - "-"
      - " "
  - file: 'https://raw.githubusercontent.com/sagdusmir/G32-Grill-Display-480x320-BTpref/main/fonts/DESG07/DSEG7ClassicMini-Bold.ttf'
    # file: 'fonts/DESG07/DSEG7ClassicMini-Bold.ttf'
    id: SEGMENT_FONT_20
    size: 20
    glyphs:
      - "0"
      - "1"
      - "2"
      - "3"
      - "4"
      - "5"
      - "6"
      - "7"
      - "8"
      - "9"
      - "-"
      - "."
      - ":"
      - " "
  - file: 'https://raw.githubusercontent.com/sagdusmir/G32-Grill-Display-480x320-BTpref/main/fonts/DESG07/DSEG7ClassicMini-Bold.ttf'
    # file: 'fonts/DESG07/DSEG7ClassicMini-Bold.ttf'
    id: SEGMENT_FONT_14
    size: 14
    glyphs:
      - "0"
      - "1"
      - "2"
      - "3"
      - "4"
      - "5"
      - "6"
      - "7"
      - "8"
      - "9"
      - "-"
      - " "
  - file: 'https://raw.githubusercontent.com/sagdusmir/G32-Grill-Display-480x320-BTpref/main/fonts/DESG07/DSEG7ClassicMini-Bold.ttf'
    # file: 'fonts/DESG07/DSEG7ClassicMini-Bold.ttf'
    id: SEGMENT_FONT_8
    size: 8
    glyphs:
      - "0"
      - "1"
      - "2"
      - "3"
      - "4"
      - "5"
      - "6"
      - "7"
      - "8"
      - "9"
  - file: 'https://raw.githubusercontent.com/sagdusmir/G32-Grill-Display-480x320-BTpref/main/fonts/Montserrat/Montserrat-Bold.ttf'
    # file: 'fonts/Montserrat/Montserrat-Bold.ttf'
    id: MONTSERRAT_BOLD_FONT_22
    size: 22
    glyphs:
      - "G"
      - "3"
      - "2"
      - " "
      - "C"
      - "o"
      - "n"
      - "e"
      - "c"
      - "t"
      - "d"
  - file: 'https://raw.githubusercontent.com/sagdusmir/G32-Grill-Display-480x320-BTpref/main/fonts/Montserrat/Montserrat-Bold.ttf'
    # file: 'fonts/Montserrat/Montserrat-Bold.ttf'
    id: MONTSERRAT_BOLD_FONT_18
    size: 18
    glyphs:
      - "0"
      - "1"
      - "2"
      - "3"
      - "4"
      - "5"
      - "6"
      - "7"
      - "8"
      - "9"
      - " "
      - "-"
      - "("
      - ")"
      - "a"
      - "b"
      - "c"
      - "d"
      - "e"
      - "f"
      - "g"
      - "h"
      - "i"
      - "j"
      - "k"
      - "l"
      - "m"
      - "n"
      - "o"
      - "p"
      - "q"
      - "r"
      - "s"
      - "t"
      - "u"
      - "v"
      - "w"
      - "x"
      - "y"
      - "z"
  - file: 'https://raw.githubusercontent.com/sagdusmir/G32-Grill-Display-480x320-BTpref/main/fonts/Montserrat/Montserrat-Bold.ttf'
    # file: 'fonts/Montserrat/Montserrat-Bold.ttf'
    id: MONTSERRAT_BOLD_FONT_14
    size: 14
    glyphs:
      - "Z"
      - "O"
      - "N"
      - "E"
      - "S"
      - "R"
      - "T"
      - "M"
      - "P"
      - "A"
      - "U"
      - "B"
      - "I"
      - "W"
      - "C"
      - "D"
      - "L"
      - "G"
      - "1"
      - "2"
      - "3"
      - "4"
      - " "

#-------------------------------------------
# Time platform
#-------------------------------------------
time:
  id: my_time

  # use public ntp servers so we can get along without Home Assistant
  platform: sntp
  # alternatively
  # platform: homeassistant

  # timezone: "Europe/Berlin"  # should be detected automatically during build process
  on_time_sync:
    - script.execute: time_update
  on_time:
    - seconds: '*'
      then:
        - script.execute: time_update

#-------------------------------------------
# LVGL library for displays
#-------------------------------------------
lvgl:
  draw_rounding: 8 # necessary for the axs15231 display controller
  buffer_size: 50%
  displays: my_display
  touchscreens: my_touchscreen
  rotation: 90
  bg_color: 0
  border_width: 0
  outline_width: 0
  theme:
    label:
      bg_color: 0
      bg_opa: COVER
      width: 120
      text_align: CENTER
    bar:
      radius: 5
      indicator:
        radius: 5
        arc_color: red
    arc:
      radius: 5
      indicator:
        arc_rounded: false
        radius: 5
    roller:
      text_font: MONTSERRAT_20
      width: 60
      selected:
        text_font: MONTSERRAT_BOLD_FONT_18
    slider:
      bg_opa: COVER
      radius: 0
      adv_hittest: true
      border_width: 0
      indicator:
        radius: 0
      knob:
        radius: 2

    textarea:
      width: 340
      height: 30
      text_font: MONTSERRAT_18
      border_width: 1
    keyboard:
      text_color: ${COLOR_100}
      bg_color: ${COLOR_25}
      items:
        bg_color: ${COLOR_100}
        text_color: ${COLOR_25}

  style_definitions:
    - id: arc_value_style
      x: 8
      y: 15
      width: 104
      height: 104
      arc_opa: COVER
      arc_rounded: false
      arc_width: 6
    - id: arc_limit_style
      x: 13
      y: 21
      width: 94
      height: 94
      arc_opa: 100%
      arc_rounded: false
      arc_width: 3
      arc_color: 0
    - id: item_obj_style
      width: 120
      height: 120
      bg_color: 0
      pad_all: 0
      radius: 0
      outline_width: 0
      border_width: 0
      border_side: NONE
      outline_pad: 0

  # send display to idle state after timeout
  on_idle:
    timeout: !lambda "return(id(settings_display_timeout_value_persistent) * 1000);"
    then:
    - if:
        condition:
          - lambda: "return id(settings_display_timeout_value_persistent) > 0;"
        then:
          - logger.log: "Display is idle"
          - light.turn_off: backlight
          - lvgl.pause:

  # boot screen with spinner - just for fun
  top_layer:
    widgets:
      - obj:
          id: boot_screen
          x: 0
          y: 0
          width: 480
          height: 320
          bg_color: 0
          bg_opa: COVER
          radius: 0
          pad_all: 0
          border_width: 0
          widgets:
            - spinner:
                id: boot_spinner
                align: CENTER
                spin_time: 1s
                arc_length: 60deg
                arc_width: 4
                arc_color: 0
                indicator:
                  arc_color: 0  # overridden after color scheme is known
                  arc_width: 4
      - obj:
          id: status_bar_top
          x: 0
          y: 0
          width: 480
          height: 22
          bg_color: 0
          bg_opa: COVER
          pad_all: 0
          border_width: 0
          hidden: true
          radius: 0
          widgets:            
            - label: # label for entering settings
                id: cs_title
                x: 0
                y: -4
                text_font: MONTSERRAT_BOLD_FONT_22
                text_color: !lambda return lv_color_hex(id(color_100));
                text_align: LEFT
                long_mode: CLIP
                width: 185
                height: 22
                text: "G32 Connected"

                clickable: true
                on_press:
                  - if:
                      condition:
                        or:
                          - lambda: 'return lv_scr_act() == id(arcs_page)->obj;'
                      then:
                        - lvgl.page.show: settings_page

            - obj: # symbol for batter low warning
                id: battery_symbol_obj
                x: 425
                y: 0
                width: 55
                height: 22
                bg_color: 0
                pad_all: 0
                outline_width: 0
                border_width: 0
                border_side: NONE
                radius: 0
                hidden: !lambda |-
                  return id(settings_hide_soc_persistent);
                widgets:
                  - label:
                      id: battery_symbol
                      x: 3
                      y: -2
                      text_font: ICON_FONT_24
                      text_align: CENTER
                      width: 24
                      text_color: !lambda |-
                        if( id(battery_soc_value) <= id(settings_min_soc_value_persistent) ) {
                          return lv_color_hex(id(color_bad));
                        }
                        return lv_color_hex(id(color_good));
                      text: !lambda |-
                        const char* icons[4] = {"\U000F008E","\U000F12A1","\U000F12A2","\U000F12A3"};
                        float soc = id(battery_soc_value);
                        int idx = soc <= 15 ? 0 :
                            soc <= 40 ? 1 :
                            soc <= 80 ? 2 : 3;
                        return icons[idx];
                  - line:
                      id: battery_symbol_fix  # glyph scaling artefact
                      points:
                        - 12, 12
                        - 18, 12
                      line_width: 1
                      line_rounded: false
                      line_color: !lambda |-
                          float soc = id(battery_soc_value);
                          if (soc <= 40) {
                            return lv_color_hex(0x000000);
                          }
                          if( id(battery_soc_value) <= id(settings_min_soc_value_persistent) ) {
                            return lv_color_hex(id(color_bad));
                          }
                          return lv_color_hex(id(color_good));
                  - label:  # battery soc background
                      id: battery_soc_shadow
                      x: 21
                      y: 7
                      text_font: SEGMENT_FONT_8
                      text_align: RIGHT
                      width: 22
                      text_color: !lambda return lv_color_hex(id(color_00));
                      text: "188"
                  - label:
                      id: battery_soc_label
                      x: 21
                      y: 7
                      text_font: SEGMENT_FONT_8
                      text_align: RIGHT
                      bg_opa: TRANSP
                      width: 22
                      text_color: !lambda |-
                        if( id(battery_soc_value) <= id(settings_min_soc_value_persistent) ) {
                          return lv_color_hex(id(color_bad));
                        }
                        return lv_color_hex(id(color_good));
                      text: !lambda |-
                        return (to_string(static_cast<int>(id(battery_soc_value)))).c_str();
                  - label:
                      id: battery_soc_label_unit
                      x: 44
                      y: 3
                      text_font: MONTSERRAT_12
                      text_align: LEFT
                      width: 7
                      text_color: !lambda |-
                        if( id(battery_soc_value) <= id(settings_min_soc_value_persistent) ) {
                          return lv_color_hex(id(color_bad));
                        }
                        return lv_color_hex(id(color_good));
                      text: "%"
            - label: # symbol for successfull BT connection
                id: g32bt_connect_label
                x: 404
                y: -2
                text_font: ICON_FONT_24
                text_align: CENTER
                width: 24
                text_color: !lambda |-
                  if( id(g32_connected) ) {
                    return lv_color_hex(id(color_good));
                  }
                  return lv_color_hex(id(color_00));
                text: "\U000F00AF"
            - label: # symbol for successfull WIFI connection
                id: wifi_connect_label
                x: 380
                y: 0
                text_font: MONTSERRAT_18
                text_align: CENTER
                width: 24
                text_color: !lambda |-
                  if( id(wifi_connected) ) {
                    return lv_color_hex(id(color_good));
                  }
                  return lv_color_hex(id(color_00));
                text: "\uF1EB" # WIFI symbol
            - label: # symbol for 'firebox open'
                id: firebox_open_label
                x: 356
                y: 1
                text_font: MONTSERRAT_18
                text_align: CENTER
                width: 24
                text_color: !lambda |-
                  if( id(firebox_open) ) {
                    return lv_color_hex(id(color_good));
                  }
                  return lv_color_hex(id(color_00));
                text: "\uF093" # arrow up
            - label: # symbol for 'light on'
                id: light_on_label
                x: 332
                y: -2
                text_font: ICON_FONT_24
                text_align: CENTER
                width: 24
                text_color: !lambda |-
                  if( id(light_on) ) {
                    return lv_color_hex(id(color_light));
                  }
                  return lv_color_hex(id(color_00));
                text: "\U000F1A4E"
            - label:
                id: warning_on_label
                x: 308
                y: 1
                text_font: MONTSERRAT_18
                text_color: !lambda |-
                  if (millis() - id(boot_start_time) < 15000) {
                    // first 15 seconds after boot: no warning
                    return lv_color_hex(id(color_00));
                  }
                  if((id(meater_alarms_tip) > 0)
                    || (id(meater_alarms_ambient) > 0)
                    || (id(battery_soc_value) <= id(settings_min_soc_value_persistent))
                    || id(warning_on)
                    || (id(g32_connected) && (id(gas_percent) <= id(settings_min_gas_value_persistent)))
                  ) {
                    return lv_color_hex(id(color_bad));
                  }
                  return lv_color_hex(id(color_00));
                text_align: CENTER
                width: 24
                text: "\uF071"
            - label: # time background
                id: display_time_shadow
                x: 188
                y: 0
                text_font: SEGMENT_FONT_20
                text_color: !lambda return lv_color_hex(id(color_00));
                text_align: CENTER
                bg_color: 0
                width: 104
                text: "88:88:88"
                hidden: !lambda |-
                  return (!id(settings_show_time_persistent) && id(settings_hide_timer_persistent));
            - label: # time hours:minutes:seconds
                id: display_time
                x: 188
                y: 0
                text_font: SEGMENT_FONT_20
                text_color: !lambda return lv_color_hex(id(color_100));
                text_align: CENTER
                bg_opa: TRANSP
                bg_color: 0
                width: 104
                text: "00:00:00"
                hidden: !lambda |-
                  return (!id(settings_show_time_persistent) && id(settings_hide_timer_persistent));
                clickable: true
                on_press:
                  - if:
                      condition:
                        lambda: 'return !id(settings_hide_timer_persistent);'
                      then:
                        - if:
                            condition:
                              or:
                                - lambda: 'return lv_scr_act() == id(arcs_page)->obj;'
                            then:
                              - lvgl.page.show: timer_page
                            else:
                              - if:
                                  condition:
                                    or:
                                      - lambda: 'return lv_scr_act() == id(timer_page)->obj;'
                                  then:
                                    - lvgl.page.show: arcs_page

                        - if:
                            condition:
                              or:
                                - lambda: 'return lv_scr_act() == id(sensor_limits_page)->obj;'
                            then:
                              - lvgl.page.show: arcs_page
            - label:
                id: timer_value_bg
                x: 188
                y: 0
                width: 104
                bg_opa: COVER
                text_font: SEGMENT_FONT_20
                text_color: !lambda return lv_color_hex(id(color_00));
                text_align: CENTER
                text: "88:88:88"
                hidden: true
            - label:
                id: timer_icon_bg
                x: 294
                y: -1
                width: 11
                bg_opa: COVER
                text_font: ICON_FONT_14
                text_color: !lambda return lv_color_hex(id(color_00));
                text_align: LEFT
                text: "\U000F051B"
                hidden: !lambda |-
                  return id(settings_hide_timer_persistent);
            - label:
                id: timer_value
                x: 188
                y: 0
                width: 104
                bg_opa: TRANSP
                text_font: SEGMENT_FONT_20
                text_color: !lambda return lv_color_hex(id(color_100));
                text_align: CENTER
                text: "00:00:00"
                hidden: true
                clickable: true
                on_press:
                  - if:
                      condition:
                        or:
                          - lambda: 'return lv_scr_act() == id(arcs_page)->obj;'
                      then:
                        - lvgl.page.show: timer_page                
            - label:
                id: timer_icon
                x: 294
                y: -1
                width: 11
                bg_opa: COVER
                text_font: ICON_FONT_14
                text_color: !lambda return lv_color_hex(id(color_100));
                text_align: LEFT
                text: "\U000F051B"
                hidden: true
      - obj:
          id: status_bar_bottom
          x: 0
          y: 298
          width: 480
          height: 22
          bg_color: 0
          bg_opa: COVER
          pad_all: 0
          border_width: 0
          radius: 0
          hidden: "true"
          widgets:
            # gas object with gas values in % and g
            - obj:
                id: gas_level_obj
                x: 0
                y: 0
                width: 480
                height: 22
                pad_all: 0
                bg_color: 0
                border_width: 0
                radius: 0
                hidden: !lambda |-
                  return id(settings_hide_gas_level_persistent);
                widgets:
                  - label:
                      id: gas_icon
                      x: 2
                      y: 0
                      width: 20
                      height: 22
                      text_font: ICON_FONT_24
                      text_color: !lambda return lv_color_hex(id(color_100));
                      text_align: CENTER
                      text: "\U000F1358"
                  - bar:
                      id: gas_percent_bar
                      x: 30
                      y: 7
                      height: 12
                      width: 300
                      radius: 0
                      min_value: 1
                      max_value: 100
                      bg_opa: COVER
                      bg_color: !lambda return lv_color_hex(id(color_25));
                      indicator:
                        radius: 0
                        bg_color: !lambda return lv_color_hex(id(color_100)); // placeholder
                      value: !lambda |-
                        int y = id(gas_weight);
                        if( y < 0) {
                          return 0;
                        }
                        int z = id(gas_percent);
                        if( z <= id(settings_min_gas_value_persistent) ) {
                          lv_obj_set_style_bg_color(id(gas_percent_bar), lv_color_hex(id(color_bad)), LV_PART_INDICATOR);
                        } else {                          
                          lv_obj_set_style_bg_color(id(gas_percent_bar), lv_color_hex(id(color_good)), LV_PART_INDICATOR);
                        }
                        return z;
                  - label:  # 1/10
                      x: 29
                      y: 5
                      width: 32
                      height: 16
                      bg_opa: TRANSP                      
                      border_width: 2
                      radius: 4
                      border_color: 0
                      text: " "
                  - label:  # 2/10
                      x: 59
                      y: 5
                      width: 32
                      height: 16
                      bg_opa: TRANSP                      
                      border_width: 2
                      radius: 4
                      border_color: 0
                      text: " "
                  - label:  # 3/10
                      x: 89
                      y: 5
                      width: 32
                      height: 16
                      bg_opa: TRANSP                      
                      border_width: 2
                      radius: 4
                      border_color: 0
                      text: " "
                  - label:  # 4/10
                      x: 119
                      y: 5
                      width: 32
                      height: 16
                      bg_opa: TRANSP                      
                      border_width: 2
                      radius: 4
                      border_color: 0
                      text: " "
                  - label:  # 5/10
                      x: 149
                      y: 5
                      width: 32
                      height: 16
                      bg_opa: TRANSP                      
                      border_width: 2
                      radius: 4
                      border_color: 0
                      text: " "
                  - label:  # 6/10
                      x: 179
                      y: 5
                      width: 32
                      height: 16
                      bg_opa: TRANSP                      
                      border_width: 2
                      radius: 4
                      border_color: 0
                      text: " "
                  - label:  # 7/10
                      x: 209
                      y: 5
                      width: 32
                      height: 16
                      bg_opa: TRANSP                      
                      border_width: 2
                      radius: 4
                      border_color: 0
                      text: " "
                  - label:  # 8/10
                      x: 239
                      y: 5
                      width: 32
                      height: 16
                      bg_opa: TRANSP                      
                      border_width: 2
                      radius: 4
                      border_color: 0
                      text: " "
                  - label:  # 9/10
                      x: 269
                      y: 5
                      width: 32
                      height: 16
                      bg_opa: TRANSP                      
                      border_width: 2
                      radius: 4
                      border_color: 0
                      text: " "
                  - label:  #107/10
                      x: 299
                      y: 5
                      width: 32
                      height: 16
                      bg_opa: TRANSP                      
                      border_width: 2
                      radius: 4
                      border_color: 0
                      text: " "
                  - label:  # gas percent label background
                      id: gas_percent_label_shadow
                      x: 331
                      y: 6
                      text_font: SEGMENT_FONT_14
                      text_align: RIGHT
                      width: 35
                      text_color: !lambda return lv_color_hex(id(color_00));
                      text: "188"
                  - label:
                      id: gas_percent_label
                      x: 331
                      y: 6
                      bg_opa: TRANSP
                      text_font: SEGMENT_FONT_14
                      text_align: RIGHT
                      width: 35
                      text: !lambda |-
                        int y = id(gas_weight);
                        if( y < 0) {
                          return " ";
                        }
                        int z = id(gas_percent);
                        return (to_string(z)).c_str();
                      text_color: !lambda |-
                        int v = id(gas_percent);
                        if( v <= id(settings_min_gas_value_persistent) ) {
                          return lv_color_hex(id(color_bad));
                        }
                        return lv_color_hex(id(color_good));
                  - label:
                      id: gas_percent_label_unit
                      x: 372
                      y: 3
                      text_font: MONTSERRAT_18
                      text_align: LEFT
                      width: 20
                      height: 19
                      text: "%"
                      text_color: !lambda |-
                        int y = id(gas_weight);
                        if( y < 0) {
                          return lv_color_hex(id(color_100));
                        }
                        int z = id(gas_percent);
                        if( z <= id(settings_min_gas_value_persistent) ) {
                          return lv_color_hex(id(color_bad));
                        }
                        return lv_color_hex(id(color_good));
                  - label:  # gas weight label background
                      id: gas_weight_label_shadow
                      x: 394
                      y: 6
                      width: 55
                      text_font: SEGMENT_FONT_14
                      text_align: RIGHT
                      text_color: !lambda return lv_color_hex(id(color_00));
                      text: "18888"
                  - label:
                      id: gas_weight_label
                      x: 394
                      y: 6
                      width: 55
                      bg_opa: TRANSP
                      text_font: SEGMENT_FONT_14
                      text_color: !lambda return lv_color_hex(id(color_100));
                      text_align: RIGHT
                      text: !lambda |-
                        int v = id(gas_weight);
                        if( v < 0) {
                          return " ";
                        }
                        return (to_string(v)).c_str();
                  - label:
                      id: gas_weight_symbol
                      x: 455
                      y: 1
                      text_font: ICON_FONT_24
                      text_color: !lambda return lv_color_hex(id(color_100));
                      text_align: LEFT
                      width: 20
                      height: 20
                      text: "\U000F0D3F"

      - obj:
          id: settings_status_bar_top
          x: 0
          y: 0
          width: 480
          height: 22
          bg_color: 0
          bg_opa: COVER
          pad_all: 0
          border_width: 0
          hidden: "true"
          radius: 0
          widgets:
            - obj:
                id: settings_status_bar_top_bar
                x: 0
                y: 4
                width: 480
                height: 18
                border_color: !lambda return lv_color_hex(id(color_75));
                border_width: 10
                border_side:
                  - TOP
                radius: 10
                pad_all: 0
                bg_color: 0
            - label:
                id: settings_status_bar_top_title
                x: 195
                y: 0
                width: 90
                bg_opa: COVER
                text_font: MONTSERRAT_BOLD_FONT_14
                text_color: !lambda return lv_color_hex(id(color_75));
                text_align: CENTER
                text: "SETTINGS"
                clickable: true
                on_press:
                  - script.execute: apply_mac_address
                  - script.execute: show_temperatures_page

            - label: # version
                id: settings_status_bar_top_version
                x: 260
                y: 4
                width: 200
                text_font: MONTSERRAT_10
                text_color: !lambda return lv_color_hex(id(color_25));
                text_align: RIGHT
                bg_opa: TRANSP
                text: ${version}
                clickable: true
                on_press:
                  - lvgl.widget.show: settings_about
      - obj:
          id: settings_about
          x: 0
          y: 22
          width: 480
          height: 298
          bg_color: 0
          bg_opa: COVER
          pad_all: 0
          border_width: 0
          hidden: "true"
          radius: 0
          clickable: true
          on_press:
            - lvgl.widget.hide: settings_about
          widgets:            
            - label:
                id: latest_version_label1
                x: 10
                y: 180
                width: 220
                text_align: LEFT
                text_color: !lambda return lv_color_hex(id(color_good));
                text_font: MONTSERRAT_14
                text: "Latest version"
                hidden: !lambda |-
                  std::string v = "${version}";
                  std::string v_latest = id(latest_version);
                  return (v == v_latest);
            - label:
                id: latest_version_label2
                x: 10
                y: 200
                width: 220
                text_align: LEFT
                text_color: !lambda return lv_color_hex(id(color_good));
                text_font: MONTSERRAT_14
                text: !lambda |-
                  return id(latest_version).c_str();
                hidden: !lambda |-
                  std::string v = "${version}";
                  std::string v_latest = id(latest_version);
                  return (v == v_latest);
            - label:
                id: current_version_label1
                x: 10
                y: 240
                width: 220
                text_align: LEFT
                text_color: !lambda return lv_color_hex(id(color_75));
                text_font: MONTSERRAT_14
                text: "Current version"
            - label:
                id: current_version_label2
                x: 10
                y: 260
                width: 220
                text_align: LEFT
                text_color: !lambda return lv_color_hex(id(color_75));
                text_font: MONTSERRAT_14
                text: ${version}
            - label:
                id: current_wifi_ip_label
                x: 10
                y: 24
                width: 220
                text_align: LEFT
                text_color: !lambda return lv_color_hex(id(color_75));
                text_font: MONTSERRAT_14
                text: !lambda |-
                  return id(current_ip_address).c_str();
            - qrcode:
                x: 230
                y: 24
                size: 250
                width: 250
                height: 250
                light_color: 0xbfbfbf
                dark_color: 0x000000
                text: ${url_qrcode}
                clickable: true
                on_press:
                  - lvgl.widget.hide: settings_about

      - keyboard:
          id: my_keyboard
          align: BOTTOM_MID
          hidden: true
          on_ready:
            - lvgl.widget.hide: my_keyboard
  pages:
    - id: arcs_page
      bg_color: 0
      bg_opa: COVER
      pad_all: 0
      widgets:
        - obj:  # only for drawing the horizontal divider
            id: zones_bar
            x: 0
            y: 32
            width: 480
            height: 20
            border_color: !lambda return lv_color_hex(id(color_75));
            border_width: 10
            border_side:
              - TOP
            radius: 10
            pad_all: 0
            bg_color: 0
        - label:
            id: zones_title
            x: 210
            y: 28
            width: 62
            bg_opa: COVER
            text_font: MONTSERRAT_BOLD_FONT_14
            text_align: CENTER
            text_color: !lambda return lv_color_hex(id(color_75));
            text: "ZONES"

        - obj:  # zones
            x: 0
            y: 42
            width: 480
            height: 123
            pad_all: 0
            border_width: 0
            radius: 0
            bg_color: 0
            widgets:
              - obj:  # zone 1
                  id: zone1_obj
                  x: 0
                  y: 0
                  styles: item_obj_style
                  clickable: !lambda |-
                    return id(settings_enable_temperature_limits_persistent);
                  on_press:
                    - lambda: |-
                        id(sensor_index) = 1;
                        id(sensor_max_value) = ${Zone_Max};
                        id(sensor_limit_value) = id(zone1_limit_value);
                        lv_slider_set_range(sensor_limit_slider, 0, ${Zone_Max});
                        lv_slider_set_value(sensor_limit_slider, id(zone1_limit_value), LV_ANIM_OFF );
                    - lvgl.label.update:
                        id: sensor_limit_headline_label
                        text: !lambda |-
                          return "ZONE 1 ALARM";
                    - lvgl.label.update:
                        id: sensor_limit_label
                        text: !lambda |-
                          return (to_string(static_cast<int>(id(zone1_limit_value)))+"°C").c_str();
                    - lvgl.widget.redraw:
                        id: sensor_limit_slider
                    - lvgl.page.show: sensor_limits_page
                  widgets:
                    - label:
                        id: zone1_obj_unit
                        x: 0
                        y: 96
                        text_font: MONTSERRAT_14
                        text: '°C'
                        text_color: !lambda return lv_color_hex(id(color_75));
                    - label:  # background
                        id: zone1_label_shadow
                        x: 17
                        y: 40
                        width: 70
                        text_font: SEGMENT_FONT_22
                        text: "888"
                        text_color: !lambda return lv_color_hex(id(color_00));
                        text_align: RIGHT
                        hidden: !lambda |-
                          return !id(settings_enable_temperature_limits_persistent) ||
                            (id(settings_enable_auto_hiding_temperature_limits_persistent) && !id(zone1_limit_value));
                    - label:
                        id: zone1_label
                        x: 17
                        y: 40
                        width: 70
                        bg_opa: TRANSP
                        text_align: RIGHT
                        text_font: SEGMENT_FONT_22
                        text_color: !lambda |-
                          if( (id(zone1_limit_value) != 0) && (id(zone1_value) >= id(zone1_limit_value)) ) {
                            return lv_color_hex(id(color_bad));
                          }
                          return lv_color_hex(id(color_100));
                        text: !lambda |-
                          if( id(zone1_value) >= ${Invalid_Sensor_Value}) {
                            return ("---");
                          }
                          return (to_string(static_cast<int>(id(zone1_value)))).c_str();
                        hidden: !lambda |-
                          return !id(settings_enable_temperature_limits_persistent) ||
                            (id(settings_enable_auto_hiding_temperature_limits_persistent) && !id(zone1_limit_value));
                    - label:  # background large
                        id: zone1_label_large_shadow
                        x: 14
                        y: 48
                        width: 90
                        text_font: SEGMENT_FONT_35
                        text: "888"
                        text_color: !lambda return lv_color_hex(id(color_00));
                        text_align: RIGHT
                        hidden: !lambda |-
                          return !(!id(settings_enable_temperature_limits_persistent) ||
                            (id(settings_enable_auto_hiding_temperature_limits_persistent) && !id(zone1_limit_value)));
                    - label:
                        id: zone1_label_large
                        x: 14
                        y: 48
                        width: 90
                        bg_opa: TRANSP
                        text_align: RIGHT
                        text_font: SEGMENT_FONT_35
                        text_color: !lambda |-
                          if( (id(zone1_limit_value) != 0) && (id(zone1_value) >= id(zone1_limit_value)) ) {
                            return lv_color_hex(id(color_bad));
                          }
                          return lv_color_hex(id(color_100));
                        text: !lambda |-
                          if( id(zone1_value) >= ${Invalid_Sensor_Value}) {
                            return ("---");
                          }
                          return (to_string(static_cast<int>(id(zone1_value)))).c_str();
                        hidden: !lambda |-
                          return !(!id(settings_enable_temperature_limits_persistent) ||
                            (id(settings_enable_auto_hiding_temperature_limits_persistent) && !id(zone1_limit_value)));
                    - label:  # alarm bell
                        id: zone1_limit_label_bell
                        x: 87
                        y: 68
                        width: 15
                        text_font: ICON_FONT_12
                        text_align: LEFT
                        text: "\U000F009A"
                        text_color: !lambda |-
                          if ( id(zone1_limit_value) != 0) {
                            return lv_color_hex(id(color_100));
                          }
                          return lv_color_hex(id(color_00));
                        hidden: !lambda |-
                          return !id(settings_enable_temperature_limits_persistent) ||
                            (id(settings_enable_auto_hiding_temperature_limits_persistent) && !id(zone1_limit_value));
                    - label:  # background
                        id: zone1_limit_label_shadow
                        x: 17
                        y: 68
                        width: 70
                        text_font: SEGMENT_FONT_22
                        text_align: RIGHT
                        text: "888"
                        text_color: !lambda return lv_color_hex(id(color_00));
                        hidden: !lambda |-
                          return !id(settings_enable_temperature_limits_persistent) ||
                            (id(settings_enable_auto_hiding_temperature_limits_persistent) && !id(zone1_limit_value));
                    - label:
                        id: zone1_limit_label
                        x: 17
                        y: 68
                        width: 70
                        bg_opa: TRANSP
                        text_font: SEGMENT_FONT_22
                        text_align: RIGHT
                        text_color: !lambda return lv_color_hex(id(color_100));
                        text: !lambda |-
                          if( id(zone1_limit_value) == 0 ) {
                            return (" ");
                          }
                          return (to_string(static_cast<int>(id(zone1_limit_value)))).c_str();
                        hidden: !lambda |-
                          return !id(settings_enable_temperature_limits_persistent) ||
                            (id(settings_enable_auto_hiding_temperature_limits_persistent) && !id(zone1_limit_value));
                    - arc:
                        id: zone1_arc
                        styles: arc_value_style
                        arc_color: !lambda return lv_color_hex(id(color_25));
                        min_value: 1
                        max_value: ${Zone_Max}
                        indicator:
                          arc_color: !lambda return lv_color_hex(id(color_100));
                          arc_width: 6
                        value: !lambda |-
                          if( id(zone1_value) >= ${Invalid_Sensor_Value} ) {
                            return 0;
                          }
                          return id(zone1_value);
                    - arc:
                        id: zone1_limit_arc
                        styles: arc_limit_style
                        min_value: 1
                        max_value: ${Zone_Max}
                        indicator:
                          arc_color: !lambda return lv_color_hex(id(color_100));
                          arc_opa: 75%
                          arc_width: 3
                        value: !lambda return id(zone1_limit_value);
                        hidden: !lambda |-
                          return !id(settings_enable_temperature_limits_persistent) ||
                            (id(settings_enable_auto_hiding_temperature_limits_persistent) && !id(zone1_limit_value));
              - obj:  # zone 2
                  id: zone2_obj
                  x: 120
                  y: 0
                  styles: item_obj_style
                  clickable: !lambda |-
                    return id(settings_enable_temperature_limits_persistent);
                  on_press:
                    - lambda: |-
                        id(sensor_index) = 2;
                        id(sensor_max_value) = ${Zone_Max};
                        id(sensor_limit_value) = id(zone2_limit_value);
                        lv_slider_set_range(sensor_limit_slider, 0, ${Zone_Max});
                        lv_slider_set_value(sensor_limit_slider, id(zone2_limit_value), LV_ANIM_OFF );
                    - lvgl.label.update:
                        id: sensor_limit_headline_label
                        text: !lambda |-
                          return "ZONE 2 ALARM";
                    - lvgl.label.update:
                        id: sensor_limit_label
                        text: !lambda |-
                          return (to_string(static_cast<int>(id(zone2_limit_value)))+"°C").c_str();
                    - lvgl.widget.redraw:
                        id: sensor_limit_slider
                    - lvgl.page.show: sensor_limits_page
                  widgets:
                    - label:
                        id: zone2_obj_unit
                        x: 0
                        y: 96
                        text_font: MONTSERRAT_14
                        text: '°C'
                        text_color: !lambda return lv_color_hex(id(color_75));
                    - label:  # background
                        id: zone2_label_shadow
                        x: 17
                        y: 40
                        width: 70
                        text_font: SEGMENT_FONT_22
                        text: "888"
                        text_color: !lambda return lv_color_hex(id(color_00));
                        text_align: RIGHT
                        hidden: !lambda |-
                          return !id(settings_enable_temperature_limits_persistent) ||
                            (id(settings_enable_auto_hiding_temperature_limits_persistent) && !id(zone2_limit_value));
                    - label:
                        id: zone2_label
                        x: 17
                        y: 40
                        width: 70
                        bg_opa: TRANSP
                        text_align: RIGHT
                        text_font: SEGMENT_FONT_22
                        text_color: !lambda |-
                          if( (id(zone2_limit_value) != 0) && (id(zone2_value) >= id(zone2_limit_value)) ) {
                            return lv_color_hex(id(color_bad));
                          }
                          return lv_color_hex(id(color_100));
                        text: !lambda |-
                          if( id(zone2_value) >= ${Invalid_Sensor_Value}) {
                            return ("---");
                          }
                          return (to_string(static_cast<int>(id(zone2_value)))).c_str();
                        hidden: !lambda |-
                          return !id(settings_enable_temperature_limits_persistent) ||
                            (id(settings_enable_auto_hiding_temperature_limits_persistent) && !id(zone2_limit_value));
                    - label:  # background large
                        id: zone2_label_large_shadow
                        x: 14
                        y: 48
                        width: 90
                        text_font: SEGMENT_FONT_35
                        text: "888"
                        text_color: !lambda return lv_color_hex(id(color_00));
                        text_align: RIGHT
                        hidden: !lambda |-
                          return !(!id(settings_enable_temperature_limits_persistent) ||
                            (id(settings_enable_auto_hiding_temperature_limits_persistent) && !id(zone2_limit_value)));
                    - label:
                        id: zone2_label_large
                        x: 14
                        y: 48
                        width: 90
                        bg_opa: TRANSP
                        text_align: RIGHT
                        text_font: SEGMENT_FONT_35
                        text_color: !lambda |-
                          if( (id(zone2_limit_value) != 0) && (id(zone2_value) >= id(zone2_limit_value)) ) {
                            return lv_color_hex(id(color_bad));
                          }
                          return lv_color_hex(id(color_100));
                        text: !lambda |-
                          if( id(zone2_value) >= ${Invalid_Sensor_Value}) {
                            return ("---");
                          }
                          return (to_string(static_cast<int>(id(zone2_value)))).c_str();
                        hidden: !lambda |-
                          return !(!id(settings_enable_temperature_limits_persistent) ||
                            (id(settings_enable_auto_hiding_temperature_limits_persistent) && !id(zone2_limit_value)));
                    - label:  # alarm bell
                        id: zone2_limit_label_bell
                        x: 87
                        y: 68
                        width: 15
                        text_font: ICON_FONT_12
                        text_align: LEFT
                        text: "\U000F009A"
                        text_color: !lambda |-
                          if ( id(zone2_limit_value) != 0) {
                            return lv_color_hex(id(color_100));
                          }
                          return lv_color_hex(id(color_00));
                        hidden: !lambda |-
                          return !id(settings_enable_temperature_limits_persistent) ||
                            (id(settings_enable_auto_hiding_temperature_limits_persistent) && !id(zone2_limit_value));
                    - label:  # background
                        id: zone2_limit_label_shadow
                        x: 17
                        y: 68
                        width: 70
                        text_font: SEGMENT_FONT_22
                        text_align: RIGHT
                        text: "888"
                        text_color: !lambda return lv_color_hex(id(color_00));
                        hidden: !lambda |-
                          return !id(settings_enable_temperature_limits_persistent) ||
                            (id(settings_enable_auto_hiding_temperature_limits_persistent) && !id(zone2_limit_value));
                    - label:
                        id: zone2_limit_label
                        x: 17
                        y: 68
                        width: 70
                        bg_opa: TRANSP
                        text_font: SEGMENT_FONT_22
                        text_align: RIGHT
                        text_color: !lambda return lv_color_hex(id(color_100));
                        text: !lambda |-
                          if( id(zone2_limit_value) == 0 ) {
                            return (" ");
                          }
                          return (to_string(static_cast<int>(id(zone2_limit_value)))).c_str();
                        hidden: !lambda |-
                          return !id(settings_enable_temperature_limits_persistent) ||
                            (id(settings_enable_auto_hiding_temperature_limits_persistent) && !id(zone2_limit_value));
                    - arc:
                        id: zone2_arc
                        styles: arc_value_style
                        arc_color: !lambda return lv_color_hex(id(color_25));
                        min_value: 1
                        max_value: ${Zone_Max}
                        indicator:
                          arc_color: !lambda return lv_color_hex(id(color_100));
                          arc_width: 6
                        value: !lambda |-
                          if( id(zone2_value) >= ${Invalid_Sensor_Value} ) {
                            return 0;
                          }
                          return id(zone2_value);
                    - arc:
                        id: zone2_limit_arc
                        styles: arc_limit_style
                        min_value: 1
                        max_value: ${Zone_Max}
                        indicator:
                          arc_color: !lambda return lv_color_hex(id(color_100));
                          arc_opa: 75%
                          arc_width: 3
                        value: !lambda return id(zone2_limit_value);
                        hidden: !lambda |-
                          return !id(settings_enable_temperature_limits_persistent) ||
                            (id(settings_enable_auto_hiding_temperature_limits_persistent) && !id(zone2_limit_value));
              - obj:  # zone 3
                  id: zone3_obj
                  x: 240
                  y: 0
                  styles: item_obj_style
                  clickable: !lambda |-
                    return id(settings_enable_temperature_limits_persistent);
                  on_press:
                    - lambda: |-
                        id(sensor_index) = 3;
                        id(sensor_max_value) = ${Zone_Max};
                        id(sensor_limit_value) = id(zone3_limit_value);
                        lv_slider_set_range(sensor_limit_slider, 0, ${Zone_Max});
                        lv_slider_set_value(sensor_limit_slider, id(zone3_limit_value), LV_ANIM_OFF );
                    - lvgl.label.update:
                        id: sensor_limit_headline_label
                        text: !lambda |-
                          return "ZONE 3 ALARM";
                    - lvgl.label.update:
                        id: sensor_limit_label
                        text: !lambda |-
                          return (to_string(static_cast<int>(id(zone3_limit_value)))+"°C").c_str();
                    - lvgl.widget.redraw:
                        id: sensor_limit_slider
                    - lvgl.page.show: sensor_limits_page
                  widgets:
                    - label:
                        id: zone3_obj_unit
                        x: 0
                        y: 96
                        text_font: MONTSERRAT_14
                        text: '°C'
                        text_color: !lambda return lv_color_hex(id(color_75));
                    - label:  # background
                        id: zone3_label_shadow
                        x: 17
                        y: 40
                        width: 70
                        text_font: SEGMENT_FONT_22
                        text: "888"
                        text_color: !lambda return lv_color_hex(id(color_00));
                        text_align: RIGHT
                        hidden: !lambda |-
                          return !id(settings_enable_temperature_limits_persistent) ||
                            (id(settings_enable_auto_hiding_temperature_limits_persistent) && !id(zone3_limit_value));
                    - label:
                        id: zone3_label
                        x: 17
                        y: 40
                        width: 70
                        bg_opa: TRANSP
                        text_align: RIGHT
                        text_font: SEGMENT_FONT_22
                        text_color: !lambda |-
                          if( (id(zone3_limit_value) != 0) && (id(zone3_value) >= id(zone3_limit_value)) ) {
                            return lv_color_hex(id(color_bad));
                          }
                          return lv_color_hex(id(color_100));
                        text: !lambda |-
                          if( id(zone3_value) >= ${Invalid_Sensor_Value}) {
                            return ("---");
                          }
                          return (to_string(static_cast<int>(id(zone3_value)))).c_str();
                        hidden: !lambda |-
                          return !id(settings_enable_temperature_limits_persistent) ||
                            (id(settings_enable_auto_hiding_temperature_limits_persistent) && !id(zone3_limit_value));
                    - label:  # background large
                        id: zone3_label_large_shadow
                        x: 14
                        y: 48
                        width: 90
                        text_font: SEGMENT_FONT_35
                        text: "888"
                        text_color: !lambda return lv_color_hex(id(color_00));
                        text_align: RIGHT
                        hidden: !lambda |-
                          return !(!id(settings_enable_temperature_limits_persistent) ||
                            (id(settings_enable_auto_hiding_temperature_limits_persistent) && !id(zone3_limit_value)));
                    - label:
                        id: zone3_label_large
                        x: 14
                        y: 48
                        width: 90
                        bg_opa: TRANSP
                        text_align: RIGHT
                        text_font: SEGMENT_FONT_35
                        text_color: !lambda |-
                          if( (id(zone3_limit_value) != 0) && (id(zone3_value) >= id(zone3_limit_value)) ) {
                            return lv_color_hex(id(color_bad));
                          }
                          return lv_color_hex(id(color_100));
                        text: !lambda |-
                          if( id(zone3_value) >= ${Invalid_Sensor_Value}) {
                            return ("---");
                          }
                          return (to_string(static_cast<int>(id(zone3_value)))).c_str();
                        hidden: !lambda |-
                          return !(!id(settings_enable_temperature_limits_persistent) ||
                            (id(settings_enable_auto_hiding_temperature_limits_persistent) && !id(zone3_limit_value)));
                    - label:  # alarm bell
                        id: zone3_limit_label_bell
                        x: 87
                        y: 68
                        width: 15
                        text_font: ICON_FONT_12
                        text_align: LEFT
                        text: "\U000F009A"
                        text_color: !lambda |-
                          if ( id(zone3_limit_value) != 0) {
                            return lv_color_hex(id(color_100));
                          }
                          return lv_color_hex(id(color_00));
                        hidden: !lambda |-
                          return !id(settings_enable_temperature_limits_persistent) ||
                            (id(settings_enable_auto_hiding_temperature_limits_persistent) && !id(zone3_limit_value));
                    - label:  # background
                        id: zone3_limit_label_shadow
                        x: 17
                        y: 68
                        width: 70
                        text_font: SEGMENT_FONT_22
                        text_align: RIGHT
                        text: "888"
                        text_color: !lambda return lv_color_hex(id(color_00));
                        hidden: !lambda |-
                          return !id(settings_enable_temperature_limits_persistent) ||
                            (id(settings_enable_auto_hiding_temperature_limits_persistent) && !id(zone3_limit_value));
                    - label:
                        id: zone3_limit_label
                        x: 17
                        y: 68
                        width: 70
                        bg_opa: TRANSP
                        text_font: SEGMENT_FONT_22
                        text_align: RIGHT
                        text_color: !lambda return lv_color_hex(id(color_100));
                        text: !lambda |-
                          if( id(zone3_limit_value) == 0 ) {
                            return (" ");
                          }
                          return (to_string(static_cast<int>(id(zone3_limit_value)))).c_str();
                        hidden: !lambda |-
                          return !id(settings_enable_temperature_limits_persistent) ||
                            (id(settings_enable_auto_hiding_temperature_limits_persistent) && !id(zone3_limit_value));
                    - arc:
                        id: zone3_arc
                        styles: arc_value_style
                        arc_color: !lambda return lv_color_hex(id(color_25));
                        min_value: 1
                        max_value: ${Zone_Max}
                        indicator:
                          arc_color: !lambda return lv_color_hex(id(color_100));
                          arc_width: 6
                        value: !lambda |-
                          if( id(zone3_value) >= ${Invalid_Sensor_Value} ) {
                            return 0;
                          }
                          return id(zone3_value);
                    - arc:
                        id: zone3_limit_arc
                        styles: arc_limit_style
                        min_value: 1
                        max_value: ${Zone_Max}
                        indicator:
                          arc_color: !lambda return lv_color_hex(id(color_100));
                          arc_opa: 75%
                          arc_width: 3
                        value: !lambda return id(zone3_limit_value);
                        hidden: !lambda |-
                          return !id(settings_enable_temperature_limits_persistent) ||
                            (id(settings_enable_auto_hiding_temperature_limits_persistent) && !id(zone3_limit_value));
              - obj:  # zone 4
                  id: zone4_obj
                  x: 360
                  y: 0
                  styles: item_obj_style
                  clickable: !lambda |-
                    return id(settings_enable_temperature_limits_persistent);
                  on_press:
                    - lambda: |-
                        id(sensor_index) = 4;
                        id(sensor_max_value) = ${Zone_Max};
                        id(sensor_limit_value) = id(zone4_limit_value);
                        lv_slider_set_range(sensor_limit_slider, 0, ${Zone_Max});
                        lv_slider_set_value(sensor_limit_slider, id(zone4_limit_value), LV_ANIM_OFF );
                    - lvgl.label.update:
                        id: sensor_limit_headline_label
                        text: !lambda |-
                          return "ZONE 4 ALARM";
                    - lvgl.label.update:
                        id: sensor_limit_label
                        text: !lambda |-
                          return (to_string(static_cast<int>(id(zone4_limit_value)))+"°C").c_str();
                    - lvgl.widget.redraw:
                        id: sensor_limit_slider
                    - lvgl.page.show: sensor_limits_page
                  widgets:
                    - label:
                        id: zone4_obj_unit
                        x: 0
                        y: 96
                        text_font: MONTSERRAT_14
                        text: '°C'
                        text_color: !lambda return lv_color_hex(id(color_75));
                    - label:  # background
                        id: zone4_label_shadow
                        x: 17
                        y: 40
                        width: 70
                        text_font: SEGMENT_FONT_22
                        text: "888"
                        text_color: !lambda return lv_color_hex(id(color_00));
                        text_align: RIGHT
                        hidden: !lambda |-
                          return !id(settings_enable_temperature_limits_persistent) ||
                            (id(settings_enable_auto_hiding_temperature_limits_persistent) && !id(zone4_limit_value));
                    - label:
                        id: zone4_label
                        x: 17
                        y: 40
                        width: 70
                        bg_opa: TRANSP
                        text_align: RIGHT
                        text_font: SEGMENT_FONT_22
                        text_color: !lambda |-
                          if( (id(zone4_limit_value) != 0) && (id(zone4_value) >= id(zone4_limit_value)) ) {
                            return lv_color_hex(id(color_bad));
                          }
                          return lv_color_hex(id(color_100));
                        text: !lambda |-
                          if( id(zone4_value) >= ${Invalid_Sensor_Value}) {
                            return ("---");
                          }
                          return (to_string(static_cast<int>(id(zone4_value)))).c_str();
                        hidden: !lambda |-
                          return !id(settings_enable_temperature_limits_persistent) ||
                            (id(settings_enable_auto_hiding_temperature_limits_persistent) && !id(zone4_limit_value));
                    - label:  # background large
                        id: zone4_label_large_shadow
                        x: 14
                        y: 48
                        width: 90
                        text_font: SEGMENT_FONT_35
                        text: "888"
                        text_color: !lambda return lv_color_hex(id(color_00));
                        text_align: RIGHT
                        hidden: !lambda |-
                          return !(!id(settings_enable_temperature_limits_persistent) ||
                            (id(settings_enable_auto_hiding_temperature_limits_persistent) && !id(zone4_limit_value)));
                    - label:
                        id: zone4_label_large
                        x: 14
                        y: 48
                        width: 90
                        bg_opa: TRANSP
                        text_align: RIGHT
                        text_font: SEGMENT_FONT_35
                        text_color: !lambda |-
                          if( (id(zone4_limit_value) != 0) && (id(zone4_value) >= id(zone4_limit_value)) ) {
                            return lv_color_hex(id(color_bad));
                          }
                          return lv_color_hex(id(color_100));
                        text: !lambda |-
                          if( id(zone4_value) >= ${Invalid_Sensor_Value}) {
                            return ("---");
                          }
                          return (to_string(static_cast<int>(id(zone4_value)))).c_str();
                        hidden: !lambda |-
                          return !(!id(settings_enable_temperature_limits_persistent) ||
                            (id(settings_enable_auto_hiding_temperature_limits_persistent) && !id(zone4_limit_value)));
                    - label:  # alarm bell
                        id: zone4_limit_label_bell
                        x: 87
                        y: 68
                        width: 15
                        bg_opa: TRANSP
                        text_font: ICON_FONT_12
                        text_align: LEFT
                        text: "\U000F009A"
                        text_color: !lambda |-
                          if ( id(zone4_limit_value) != 0) {
                            return lv_color_hex(id(color_100));
                          }
                          return lv_color_hex(id(color_00));
                        hidden: !lambda |-
                          return !id(settings_enable_temperature_limits_persistent) ||
                            (id(settings_enable_auto_hiding_temperature_limits_persistent) && !id(zone4_limit_value));
                    - label:  # background
                        id: zone4_limit_label_shadow
                        x: 17
                        y: 68
                        width: 70
                        text_font: SEGMENT_FONT_22
                        text_align: RIGHT
                        text: "888"
                        text_color: !lambda return lv_color_hex(id(color_00));
                        hidden: !lambda |-
                          return !id(settings_enable_temperature_limits_persistent) ||
                            (id(settings_enable_auto_hiding_temperature_limits_persistent) && !id(zone4_limit_value));
                    - label:
                        id: zone4_limit_label
                        x: 17
                        y: 68
                        width: 70
                        bg_opa: TRANSP
                        text_font: SEGMENT_FONT_22
                        text_align: RIGHT
                        text_color: !lambda return lv_color_hex(id(color_100));
                        text: !lambda |-
                          if( id(zone4_limit_value) == 0 ) {
                            return (" ");
                          }
                          return (to_string(static_cast<int>(id(zone4_limit_value)))).c_str();
                        hidden: !lambda |-
                          return !id(settings_enable_temperature_limits_persistent) ||
                            (id(settings_enable_auto_hiding_temperature_limits_persistent) && !id(zone4_limit_value));
                    - arc:
                        id: zone4_arc
                        styles: arc_value_style
                        arc_color: !lambda return lv_color_hex(id(color_25));
                        min_value: 1
                        max_value: ${Zone_Max}
                        indicator:
                          arc_color: !lambda return lv_color_hex(id(color_100));
                          arc_width: 6
                        value: !lambda |-
                          if( id(zone4_value) >= ${Invalid_Sensor_Value} ) {
                            return 0;
                          }
                          return id(zone4_value);
                    - arc:
                        id: zone4_limit_arc
                        styles: arc_limit_style
                        min_value: 1
                        max_value: ${Zone_Max}
                        indicator:
                          arc_color: !lambda return lv_color_hex(id(color_100));
                          arc_opa: 75%
                          arc_width: 3
                        value: !lambda return id(zone4_limit_value);
                        hidden: !lambda |-
                          return !id(settings_enable_temperature_limits_persistent) ||
                            (id(settings_enable_auto_hiding_temperature_limits_persistent) && !id(zone4_limit_value));

        - obj:  # only for drawing the horizontal divider
            id: probes_bar
            x: 0
            y: 165
            width: 480
            border_color: !lambda return lv_color_hex(id(color_75));
            height: 138
            border_width: 10
            border_side:
              - TOP
            radius: 10
            pad_all: 0
            bg_color: 0
        - label:
            id: probes_title
            y: 161
            bg_opa: COVER
            text_font: MONTSERRAT_BOLD_FONT_14
            text_align: CENTER
            text_color: !lambda return lv_color_hex(id(color_75));
            x: 146
            width: 188
            text: "TEMPERATURE PROBES"
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
